aidancrowther/DMX-Now/Docs/priority-packet-substantial-completion.md

# Targeted Priority Packet: Completion

**Status:** Complete for the validated Linux/20 Hz hardware configuration
**Branch:** `master`
**Date:** 2026-09-10

## Scope completed

The targeted priority packet path is implemented across the host daemon,
transmitter, receiver, and shared protocol:

- Added distinct priority and priority-completion packet types.
- Added host-to-transmitter management commands for priority marking and ACK
  retrieval.
- Added complete-universe priority transmission with repeat count, TTL, and
  bounded queueing.
- Added receiver-targeted transaction sequencing and per-receiver state.
- Added receiver completion ACK handling, duplicate/invalid/unknown ACK
  accounting, and retry/recovery behavior.
- Added runtime receiver hard-gate enforcement using a 512-byte write-permission
  table and a no-gates fast path.
- Added staged priority gate metadata with atomic application after complete
  priority reconstruction.
- Added queue-aware transmitter metadata delivery and explicit gate-application
  completion status.
- Fixed the management-interface crash when editing a hard-locked channel.
- Added lead-in and lead-out timing so priority traffic is separated from the
  normal 20 Hz DMX stream.
- Preserved normal latest-state DMX pacing outside priority transactions.
- Added host tests for service behavior and priority transaction handling.
- Added a hardware transition acceptance runner at
  `Host Software/wireless_dmx_daemon/tests/run_priority_transition.py`.

## Acceptance evidence

The following live hardware tests were completed with normal firmware on the
transmitter and all expected receivers discovered during each run:

### Targeted priority test

- 10 priority events submitted.
- Both receivers acknowledged every event.
- 10/10 first-attempt successes.
- 0 retry-recovered events.
- 0 failed events.
- 0 invalid or unknown ACKs.

### Extended priority soak

- 20 events with 10-second spacing.
- 20/20 first-attempt successes.
- Both receivers acknowledged every event.
- 0 retry-recovered events.
- 0 failed events.
- 0 invalid or unknown ACKs.
- Process exit status: `0`.

The final lab soak reported zero failed events, retry recoveries, invalid ACKs,
unknown ACKs, and retry failures. Duplicate ACK records were expected repeated physical completion
records from the receiver ACK-repeat mechanism.

### Priority-to-normal transition

The transition runner uses three separate Mega measurement windows:

1. Normal DMX output before priority.
2. Priority DMX output while the transaction is active.
3. Normal DMX output after ACK completion and a three-second settling period.

The final run passed all phases:

```text
normal before: 222 checks, 222 pass, 0 fail
priority:      311 checks, 311 pass, 0 fail
normal after:  355 checks, 355 pass, 0 fail
receiver ACKs: both expected receivers acknowledged
exit code:     0
```

The post-priority settling period is intentional. An earlier version measured
immediately at the end of the transaction and captured six transient settling
frames. Extending the settle period makes the test distinguish a bounded
transition from a persistent failure to resume normal DMX.

### Hard-gate transition

All expected receivers were included in event construction and required to
report gate application. The Mega monitor validated the physical output through the
lock and unlock transitions:

```text
normal baseline:        266 checks, 266 pass, 0 fail
priority gate establish: 266 checks, 266 pass, 0 fail
normal while locked:    266 checks, 266 pass, 0 fail
priority unlock:        267 checks, 267 pass, 0 fail
normal after unlock:    266 checks, 266 pass, 0 fail
```

Lock and unlock transactions completed on the first attempt with
`PRIORITY_COMPLETE_GATE_APPLIED` from all expected receivers and zero retries. During
the locked phase, normal packets carrying a different value were transmitted
but the receivers continued outputting the priority value. After the all-clear
priority transaction, normal output resumed.

The current 20-event soak was scoped to the expected receiver set:

```text
events: 20
first-attempt successes: 20
failed events: 0
unknown ACKs: 0
invalid ACKs: 0
retry failures: 0
```

## Automated validation

The host test suite passes in full after the current implementation changes:

```text
68 passed
```

The transition runner passes Python compilation and repository whitespace
validation.

## Running the transition test

With the transmitter and monitor connected to the selected host devices, and
the expected receiver IDs discovered or supplied for the run, execute:

```bash
cd "Host Software/wireless_dmx_daemon"
python Tests/run_priority_transition.py \
  --tx-port /dev/ttyUSB0 \
  --mega-port /dev/ttyUSB1 \
  --expected-receiver <receiver-id> \
  --output /tmp/priority-transition.json
```

The command returns zero only when normal output is valid before and after the
priority transaction, the priority output is observed, and every expected
receiver completes the transaction.

## Hardware intervention and resilience validation

The following recovery tests passed with the expected receiver set powered and online:

* receiver removal for 20 seconds followed by reconnection;
* transmitter reset while the daemon remained running;
* clean daemon stop/restart with cache clear and receiver rediscovery;
* controlled PTY client disconnect for 10 seconds followed by reconnection.

Each recovery returned to valid normal DMX output. Fresh priority transactions
after receiver reconnection, transmitter reset, daemon restart, and PTY
reconnection completed with all expected receiver ACKs on the first attempt and
zero retries.

Reliability and throughput work is complete for the validated Linux/ESP8266/Mega deployment at the
20 Hz production rate. Native Windows/macOS virtual serial support, broader
lighting-application/platform coverage, and longer optional soak runs remain
non-blocking follow-up work.

Other existing project follow-up items remain unchanged, including native
Windows/macOS virtual serial support, broader fault-injection coverage, and a
future GUI.
