aidancrowther/DMX-Now/Host Software/wireless_dmx_daemon/wireless_dmx/app.py

"""Application service coordinating adapters and frontend snapshots."""

from __future__ import annotations

import time
import logging
import random
from dataclasses import replace
from threading import Event, Thread, Lock

from .enttec.parser import EnttecParser
from .artnet import ArtNetListener, ArtNetParser
from .models import (DaemonConfig, DaemonHealth, DaemonMode, DaemonSnapshot, DmxStatistics,
    ChannelGate, ObservedUniverse, PriorityAck, PriorityAckSummary, PriorityStatus, TelemetryStatus,
    RetransmitterTelemetry)
from .pacer import DmxPacer
from .telemetry import TelemetryStore
from .transmitter.connection import TransmitterConnection
from .transmitter.management import (CacheClearedResponse, ManagementParser, PriorityAckReport,
                                     TransmitterModeResponse,
                                      clear_receiver_cache_request, get_priority_acks_request, get_telemetry_request,
                                      get_transmitter_mode_request,
                                      get_observed_universe_request, ObservedUniversePart,
                                      RetransmitterTelemetryReport,
                                      set_retransmitter_input_request, locate_retransmitter_request,
                                      mark_next_priority, set_receiver_failsafe_request, set_receiver_output_request,
                                      locate_receiver_request)
from .protocols import DMX_GATE_MASK_SIZE
from .protocols import PRIORITY_COMPLETE_GATE_APPLIED
from .virtual_serial.factory import create_pty_backend
from .raw_dmx import RawDmxParser


class NullVirtualBackend:
    """No-op backend used when virtual serial input is disabled."""

    path = ""
    client_connected = False
    master_fd = None

    def start(self) -> None:
        pass

    def read(self, size: int = 4096) -> bytes:
        return b""

    def stop(self) -> None:
        pass


class WirelessDmxService:
    def __init__(self, config: DaemonConfig, serial_factory=None, virtual_backend=None) -> None:
        config.validate()
        self.config = config
        self.stats = DmxStatistics()
        self.enttec = EnttecParser(stats=self.stats)
        self.telemetry = TelemetryStore(config.telemetry_stale_seconds, config.telemetry_offline_seconds)
        self.management = ManagementParser()
        self.virtual = virtual_backend or (create_pty_backend(config.virtual_port_path)
                                           if config.virtual_serial_enabled else NullVirtualBackend())
        self.raw_virtual = (create_pty_backend(config.raw_virtual_port_path)
                            if config.raw_virtual_serial_enabled else NullVirtualBackend())
        self.raw_dmx = RawDmxParser(config.raw_virtual_timeout_seconds)
        self.artnet_parser = ArtNetParser(config.artnet_universe, self.stats)
        self.artnet = ArtNetListener(config.artnet_bind_host, config.artnet_port, self.artnet_parser) \
            if config.artnet_enabled else None
        self.transmitter = TransmitterConnection(config, self._on_transmitter_data, serial_factory)
        self.pacer = DmxPacer(
            config.pacer_rate_hz, self._send_universe, self.stats,
            send_priority=self._send_priority_universe,
            on_priority_started=self._on_priority_started,
            on_priority_completed=self._on_priority_completed,
            priority_enabled=config.priority_enabled,
            priority_max_queue_depth=config.priority_max_queue_depth,
            priority_max_repeat_count=config.priority_max_repeat_count,
            priority_max_ttl_seconds=config.priority_max_ttl_seconds,
            priority_lead_in_ms=config.priority_lead_in_ms,
            priority_lead_out_ms=config.priority_lead_out_ms,
            priority_max_consecutive_events=config.priority_max_consecutive_events,
        )
        self.manual_universe = bytearray(512)
        self.observed_universe = ObservedUniverse()
        self._retransmitters: dict[int, tuple[RetransmitterTelemetry, float]] = {}
        self._observed_parts: dict[tuple[int, int], dict[int, ObservedUniversePart]] = {}
        self._observed_part_times: dict[tuple[int, int], float] = {}
        self._last_observed_request = 0.0
        self._channel_gates = [ChannelGate.OPEN] * 512
        self._has_source_blocked_channels = False
        self._hard_gate_metadata_pending = bool(config.locked_channels)
        for channel in config.management_only_channels:
            self._channel_gates[channel - 1] = ChannelGate.MANAGEMENT_ONLY
        for channel in config.locked_channels:
            self._channel_gates[channel - 1] = ChannelGate.LOCKED
        self._refresh_gate_fast_path()
        self._stop = Event()
        self._thread: Thread | None = None
        self._lock = Lock()
        self._health = DaemonHealth.STARTING
        self._last_error: str | None = None
        self._last_telemetry_request = 0.0
        self._last_ack_request = 0.0
        self._telemetry_request_started = 0.0
        self._telemetry_requests_sent = 0
        self._telemetry_reports_received = 0
        self._telemetry_consecutive_failures = 0
        self._telemetry_last_report = 0.0
        self._cache_clear_sent_at = 0.0
        self._cache_clear_acknowledged = False
        self._cache_clear_sent = 0
        self._cache_clear_retries = 0
        self._cache_clear_retry_interval = 0.5
        self._report_parts = {}
        self._report_part_times = {}
        self._priority_submissions: dict[int, float] = {}
        # One accepted ACK is valid per submitted event, receiver, and attempt.
        # Frame sequence is diagnostic only: repeated priority fragments/events
        # can legitimately carry different wireless frame sequences.
        self._priority_events: dict[int, dict] = {}
        # One ACK is retained per submitted event, receiver, and attempt.
        # Retry attempts are distinct evidence and must not be discarded as
        # duplicates of the initial attempt.
        self._priority_acks: dict[tuple[int, int, int], PriorityAck] = {}
        self._priority_ack_summary = PriorityAckSummary()
        self._priority_retry_attempts = 0
        self._priority_retry_recovered = 0
        self._priority_retry_failures = 0
        self._normal_quiet_until = 0.0
        self._priority_output_active = False
        self._failsafe_generation = int(time.time()) & 0xFFFFFFFF
        self._last_failsafe_send = 0.0
        self._logger = logging.getLogger("wireless_dmx.service")
        self._transmitter_mode_acknowledged = False
        self._transmitter_mode_query_pending = False
        self._transmitter_mode_set_pending = False
        self._transmitter_mode_current: int | None = None
        self._transmitter_mode_sync = "pending"
        self._transmitter_mode_request_at = 0.0
        self._last_transmitter_connected = False

    def set_manual_channel(self, channel: int, value: int) -> None:
        if not 1 <= channel <= 512:
            raise ValueError("channel must be 1..512")
        if not 0 <= value <= 255:
            raise ValueError("value must be 0..255")
        # This is a management-originated edit. LOCKED means that ordinary
        # source/retransmitter data cannot overwrite the channel; it does not
        # prevent the management interface from deliberately overriding it.
        self.manual_universe[channel - 1] = value

    def set_manual_universe(self, universe: bytes) -> None:
        if len(universe) != 512:
            raise ValueError("manual universe must contain 512 channels")
        # Full-universe edits are also management-originated and may update
        # hard-locked channels. The gate is enforced when external source data
        # is merged, not when the operator sends an explicit management value.
        self.manual_universe[:] = universe

    def channel_gate(self, channel: int) -> ChannelGate:
        if not 1 <= channel <= 512:
            raise ValueError("channel must be 1..512")
        return self._channel_gates[channel - 1]

    def set_channel_gate(self, channel: int, gate: ChannelGate) -> None:
        if not 1 <= channel <= 512:
            raise ValueError("channel must be 1..512")
        gate = ChannelGate(gate)
        previous = self._channel_gates[channel - 1]
        # In management-only mode the retransmitter is the live source. When
        # an operator establishes a hard lock, capture the value currently
        # shown by that source before future observations are intentionally
        # prevented from changing the channel. Otherwise the local management
        # buffer (often still zero) would become the receiver's locked value.
        if (gate == ChannelGate.LOCKED and previous != ChannelGate.LOCKED and
                self.config.mode == DaemonMode.MANAGEMENT_ONLY):
            self.manual_universe[channel - 1] = self.observed_universe.universe[channel - 1]
        self._channel_gates[channel - 1] = gate
        if previous != self._channel_gates[channel - 1] or gate == ChannelGate.LOCKED:
            self._hard_gate_metadata_pending = True
        self._refresh_gate_fast_path()
        management_only, locked = self.channel_gate_lists()
        self.config = replace(self.config, management_only_channels=management_only,
                              locked_channels=locked)
        self.stats.channel_gate_changes += 1

    def _refresh_gate_fast_path(self) -> None:
        self._has_source_blocked_channels = any(gate != ChannelGate.OPEN
                                                for gate in self._channel_gates)

    def channel_gates_snapshot(self) -> tuple[ChannelGate, ...]:
        return tuple(self._channel_gates)

    def channel_gate_lists(self) -> tuple[tuple[int, ...], tuple[int, ...]]:
        return (tuple(i + 1 for i, gate in enumerate(self._channel_gates)
                      if gate == ChannelGate.MANAGEMENT_ONLY),
                tuple(i + 1 for i, gate in enumerate(self._channel_gates)
                      if gate == ChannelGate.LOCKED))

    def clear_manual_universe(self) -> None:
        # Clearing from the management interface is an explicit override too.
        self.manual_universe[:] = bytes(512)

    def manual_universe_snapshot(self) -> bytes:
        return bytes(self.manual_universe)

    def observed_universe_snapshot(self) -> bytes:
        return self.observed_universe.universe

    def _update_observed_universe(self, universe: bytes, sequence: int, source: str) -> None:
        merged = bytearray(universe)
        for index, gate in enumerate(self._channel_gates):
            if gate == ChannelGate.LOCKED:
                merged[index] = self.manual_universe[index]
        self.observed_universe = ObservedUniverse(bytes(merged), sequence, source,
                                                  time.monotonic(), self.observed_universe.updates + 1)

    def _update_local_observed_universe(self, universe: bytes) -> None:
        self._update_observed_universe(universe, 0, "local transmitter")

    def send_manual(self, priority: bool = False, repeat_count: int | None = None,
                    ttl_seconds: float | None = None, reason: str = "manual dashboard") -> int | None:
        if not priority and self.config.mode == DaemonMode.MANAGEMENT_ONLY:
            self.stats.frames_dropped_by_pacer += 1
            raise RuntimeError("normal DMX transmission is disabled in management-only mode")
        universe = bytes(self.manual_universe)
        self._update_local_observed_universe(universe)
        if priority:
            hard_gate_mask = None
            if self._hard_gate_metadata_pending:
                hard_gate_mask_buffer = bytearray(DMX_GATE_MASK_SIZE)
                for index, gate in enumerate(self._channel_gates):
                    if gate == ChannelGate.LOCKED:
                        hard_gate_mask_buffer[index // 8] |= 1 << (index % 8)
                hard_gate_mask = bytes(hard_gate_mask_buffer)
                self._hard_gate_metadata_pending = False
            physical_repeat_count = repeat_count or self.config.priority_default_repeat_count
            self._normal_quiet_until = max(self._normal_quiet_until,
                time.monotonic() + self.config.priority_normal_quiet_before_ms / 1000.0)
            # The transmitter owns the three physical 1 Hz repeats. The daemon
            # submits one logical universe per attempt only.
            priority_id = self.pacer._priority_id
            self.pacer._priority_id = (priority_id + 1) & 0xFFFFFFFF
            # The marker is deliberately queued ahead of the following
            # complete-universe DMX submission. Existing receivers ignore it.
            self._priority_submissions[priority_id] = time.monotonic()
            self._priority_events[priority_id] = {
                "universe": universe, "repeat_count": physical_repeat_count,
                "hard_gate_mask": hard_gate_mask,
                "ttl_seconds": ttl_seconds or self.config.priority_default_ttl_seconds,
                "reason": reason, "attempt": 1, "last_attempt_at": time.monotonic(),
                "retry_count": 0, "terminal": False, "terminal_reason": None,
                "transmission_complete": False, "ack_complete": False,
                "first_attempt_ack_receivers": set(), "ack_receivers": set(),
                "submitted_at": time.monotonic(), "ack_completed_at": None,
                "expected_receivers": set(receiver.receiver_id for receiver in self.telemetry.snapshot()
                                           if receiver.link_state.value == "online"),
                "retry_due_at": None,
                "receiver_states": {receiver.receiver_id: {"attempt": 0, "started_at": None,
                    "ack": False, "failed": False} for receiver in
                    self.telemetry.snapshot() if receiver.link_state.value == "online"},
                "receiver_order": [receiver.receiver_id for receiver in self.telemetry.snapshot()
                                   if receiver.link_state.value == "online"],
                "receiver_index": 0, "current_receiver": None,
            }
            event = self._priority_events[priority_id]
            if event["receiver_order"]:
                self._start_priority_receiver(event, priority_id, time.monotonic())
            else:
                # Preserve the existing broadcast behavior when no fresh
                # receiver telemetry is available (including unit-test and
                # hardware-discovery bootstrap conditions).
                self.transmitter.send_immediate(mark_next_priority(
                    priority_id, physical_repeat_count, 1, 0, hard_gate_mask))
                self.pacer.submit_priority(universe, repeat_count=1,
                                           ttl_seconds=event["ttl_seconds"],
                                           reason=event["reason"], priority_id=priority_id)
            return priority_id
        self.pacer.submit(universe)
        return None

    def set_receiver_output(self, enabled: bool, receiver_id: int = 0) -> tuple[int, ...]:
        """Request a targeted or broadcast MAX3485 output change."""
        online = tuple(receiver.receiver_id for receiver in self.telemetry.snapshot()
                       if receiver.link_state.value == "online" and
                       (receiver_id == 0 or receiver.receiver_id == receiver_id))
        generation = int(time.time() * 1000) & 0xFFFFFFFF
        if receiver_id and not online:
            raise ValueError(f"receiver {receiver_id:08X} is not online")
        if not self.transmitter.connected:
            detail = self.transmitter.last_error or "serial transmitter is not connected"
            raise RuntimeError(f"output control not sent: {detail}")
        if not self.transmitter.send_priority_management(
                set_receiver_output_request(enabled, receiver_id, generation)):
            detail = self.transmitter.last_error or "priority management queue rejected the packet"
            raise RuntimeError(f"output control not sent: {detail}")
        return online

    def locate_receiver(self, receiver_id: int = 0, duration_seconds: int = 15) -> tuple[int, ...]:
        online = tuple(receiver.receiver_id for receiver in self.telemetry.snapshot()
                       if receiver.link_state.value == "online" and
                       (receiver_id == 0 or receiver.receiver_id == receiver_id))
        if receiver_id and not online:
            raise ValueError(f"receiver {receiver_id:08X} is not online")
        generation = int(time.time() * 1000) & 0xFFFFFFFF
        if not self.transmitter.connected:
            detail = self.transmitter.last_error or "serial transmitter is not connected"
            raise RuntimeError(f"locate not sent: {detail}")
        if not self.transmitter.send_priority_management(
                locate_receiver_request(receiver_id, duration_seconds, generation)):
            detail = self.transmitter.last_error or "priority management queue rejected the packet"
            raise RuntimeError(f"locate not sent: {detail}")
        return online

    def set_retransmitter_input(self, enabled: bool, retransmitter_id: int = 0) -> None:
        if not self.config.retransmitter_input_control_enabled:
            raise RuntimeError("retransmitter input control is disabled in configuration")
        generation = int(time.time() * 1000) & 0xFFFFFFFF
        if not self.transmitter.connected:
            raise RuntimeError("retransmitter input control: transmitter is disconnected")
        if not self.transmitter.send_priority_management(
                set_retransmitter_input_request(retransmitter_id, enabled, generation)):
            raise RuntimeError(self.transmitter.last_error or "retransmitter control queue rejected the packet")

    def locate_retransmitter(self, retransmitter_id: int = 0, duration_seconds: int = 15) -> None:
        generation = int(time.time() * 1000) & 0xFFFFFFFF
        if not self.transmitter.connected:
            raise RuntimeError("retransmitter locate: transmitter is disconnected")
        if not self.transmitter.send_priority_management(
                locate_retransmitter_request(retransmitter_id, duration_seconds, generation)):
            raise RuntimeError(self.transmitter.last_error or "retransmitter control queue rejected the packet")

    def clear_priority(self) -> None:
        self.pacer.clear_priority()

    def seed_priority_ids(self, seed: int) -> None:
        """Set the next priority ID before submitting any priority events."""
        with self.pacer._condition:
            if self.pacer._priority_queue or self.pacer._priority_current is not None:
                raise RuntimeError("cannot seed priority IDs while priority traffic is active")
            self.pacer._priority_id = seed & 0xFFFFFFFF

    def start(self) -> None:
        self.telemetry.clear()
        if self.config.mode == DaemonMode.BRIDGE:
            self.virtual.start()
            self.raw_virtual.start()
            if self.artnet:
                self.artnet.start()
        self.transmitter.start()
        self._send_transmitter_mode_query()
        self.pacer.start()
        self._stop.clear()
        self._thread = Thread(target=self._run, name="wireless-dmx-service", daemon=True)
        self._thread.start()
        self._health = DaemonHealth.RUNNING
        self._logger.info("service_started")

    def stop(self) -> None:
        self._health = DaemonHealth.STOPPING
        self._stop.set()
        if self._thread:
            self._thread.join(timeout=2)
        self.pacer.stop()
        self.transmitter.stop()
        if self.artnet:
            self.artnet.stop()
        if self.config.mode == DaemonMode.BRIDGE:
            self.virtual.stop()
            self.raw_virtual.stop()
        self._logger.info("service_stopped")

    def snapshot(self) -> DaemonSnapshot:
        stats = DmxStatistics(**self.stats.__dict__)
        virtual_path = self.virtual.path if getattr(self.virtual, "master_fd", None) is not None else None
        priority = self.pacer.priority_status()
        ack_summary = self._priority_ack_summary
        priority = PriorityStatus(**{**priority.__dict__,
            "ack_accepted": ack_summary.accepted_count,
            "ack_duplicates": ack_summary.duplicate_count,
            "ack_invalid": ack_summary.invalid_count,
            "ack_unknown": ack_summary.unknown_priority_count,
            "ack_duplicate_records": ack_summary.duplicate_record_count,
            "ack_dropped": ack_summary.dropped_count,
            "ack_window_failures": ack_summary.window_failure_count})
        priority = PriorityStatus(**{**priority.__dict__,
            "ack_records_received": ack_summary.records_received})
        priority = PriorityStatus(**{**priority.__dict__,
            "retry_attempts": self._priority_retry_attempts,
            "retry_recovered": self._priority_retry_recovered,
            "retry_failures": self._priority_retry_failures})
        mode_name = ("management_only" if self._transmitter_mode_current == 1 else
                      "bridge" if self._transmitter_mode_current == 0 else None)
        return DaemonSnapshot(health=self._health, virtual_port=virtual_path,
                              transmitter_connected=self.transmitter.connected,
                              virtual_client_connected=self.virtual.client_connected,
                              dmx=stats, receivers=self.telemetry.snapshot(),
                               priority=priority,
                              observed_universe=self.observed_universe,
                              retransmitters=self._retransmitter_snapshot(),
                              transmitter_mode=mode_name,
                              transmitter_mode_sync=self._transmitter_mode_sync,
                              telemetry=TelemetryStatus(
                                  enabled=self.config.telemetry_enabled,
                                  request_in_flight=self._telemetry_request_started > 0,
                                  requests_sent=self._telemetry_requests_sent,
                                  reports_received=self._telemetry_reports_received,
                                  consecutive_failures=self._telemetry_consecutive_failures,
                                  last_request_age_ms=(int((time.monotonic() - self._telemetry_request_started) * 1000)
                                                       if self._telemetry_request_started else None),
                                  last_report_age_ms=(int((time.monotonic() - self._telemetry_last_report) * 1000)
                                                       if self._telemetry_last_report else None),
                                  cache_clear_sent=self._cache_clear_sent,
                                  cache_clear_acknowledged=self._cache_clear_acknowledged,
                                  cache_clear_age_ms=(int((time.monotonic() - self._cache_clear_sent_at) * 1000)
                                                     if self._cache_clear_sent_at else None),
                                  cache_clear_retries=self._cache_clear_retries),
                              last_error=self._last_error)

    def _retransmitter_snapshot(self) -> tuple[RetransmitterTelemetry, ...]:
        now = time.monotonic()
        result = []
        for telemetry, seen in self._retransmitters.values():
            age = now - seen
            state = (type(telemetry.link_state).ONLINE if age <= self.config.telemetry_stale_seconds
                     else type(telemetry.link_state).STALE if age <= self.config.telemetry_offline_seconds
                     else type(telemetry.link_state).OFFLINE)
            # Retransmitters are discovery devices, not a retained inventory.
            # Only an actively reporting device should populate the dashboard
            # or be eligible for retransmitter controls.
            if state != type(telemetry.link_state).ONLINE:
                continue
            result.append(replace(telemetry, link_state=state,
                                  transmitter_rssi=telemetry.transmitter_rssi))
        return tuple(sorted(result, key=lambda item: item.retransmitter_id))

    def _send_cache_clear(self) -> None:
        self._cache_clear_acknowledged = False
        # Drop host-side discovery immediately; the transmitter clears both
        # receiver and retransmitter tables when it processes this request.
        self.telemetry.clear()
        self._retransmitters.clear()
        self.transmitter.send_immediate(clear_receiver_cache_request())
        self._cache_clear_sent += 1
        self._cache_clear_retries = max(0, self._cache_clear_sent - 1)
        self._cache_clear_sent_at = time.monotonic()
        self._logger.info("receiver_cache_clear_sent attempt=%s", self._cache_clear_sent)

    def _send_transmitter_mode_query(self) -> None:
        if self.transmitter.send_immediate(get_transmitter_mode_request()):
            self._transmitter_mode_query_pending = True
            self._transmitter_mode_set_pending = False
            self._transmitter_mode_request_at = time.monotonic()
            self._logger.info("transmitter_mode_query_sent")

    def _send_transmitter_mode(self) -> None:
        from .transmitter.management import set_transmitter_mode_request
        mode = 1 if self.config.mode == DaemonMode.MANAGEMENT_ONLY else 0
        if self.transmitter.send_immediate(set_transmitter_mode_request(mode)):
            self._transmitter_mode_acknowledged = False
            self._transmitter_mode_query_pending = False
            self._transmitter_mode_set_pending = True
            self._logger.info("transmitter_mode_requested mode=%s", self.config.mode.value)

    def _send_universe(self, universe: bytes) -> None:
        if self.config.mode == DaemonMode.MANAGEMENT_ONLY:
            self.stats.frames_dropped_by_pacer += 1
            return
        if self._priority_output_active or time.monotonic() < self._normal_quiet_until:
            self.stats.frames_dropped_by_pacer += 1
            return
        from .enttec.protocol import encode_dmx
        self._update_local_observed_universe(universe)
        self.transmitter.send_latest(encode_dmx(universe))

    def _send_priority_universe(self, universe: bytes) -> None:
        from .enttec.protocol import encode_dmx
        self._update_local_observed_universe(universe)
        self.transmitter.send_latest(encode_dmx(universe))

    def _start_priority_receiver(self, event: dict, priority_id: int, now: float) -> None:
        order = event.get("receiver_order", [])
        while event["receiver_index"] < len(order):
            receiver_id = order[event["receiver_index"]]
            state = event["receiver_states"][receiver_id]
            if state["ack"] or state["failed"]:
                event["receiver_index"] += 1
                continue
            if state["attempt"] >= self.config.priority_max_attempts:
                state["failed"] = True
                event["receiver_index"] += 1
                continue
            state["attempt"] += 1
            state["started_at"] = now
            event["current_receiver"] = receiver_id
            if not self.transmitter.send_priority_management(mark_next_priority(
                priority_id, event["repeat_count"], state["attempt"], receiver_id,
                event["hard_gate_mask"])):
                state["started_at"] = now
                return
            self.pacer.submit_priority(event["universe"], repeat_count=1,
                                       ttl_seconds=event["ttl_seconds"],
                                       reason=event["reason"], priority_id=priority_id,
                                       attempt=state["attempt"],
                                       target_receiver_id=receiver_id)
            return
        event["ack_complete"] = all(state["ack"] for state in event["receiver_states"].values())
        event["transmission_complete"] = True
        event["terminal_reason"] = "ack_complete" if event["ack_complete"] else "receiver_timeout"
        event["terminal"] = True

    def _on_priority_started(self) -> None:
        self._priority_output_active = True

    def _on_priority_completed(self) -> None:
        self._priority_output_active = False
        self._normal_quiet_until = max(self._normal_quiet_until,
            time.monotonic() + self.config.priority_normal_quiet_after_ms / 1000.0)

    def _accept_source_frame(self, universe: bytes, source: str) -> None:
        if self.config.mode == DaemonMode.MANAGEMENT_ONLY:
            self.stats.source_frames_rejected += 1
            self.stats.frames_dropped_by_pacer += 1
            return
        policy = self.config.input_source_policy
        if policy != "latest" and policy != source:
            self.stats.source_frames_rejected += 1
            return
        if source == "artnet":
            self.stats.artnet_source_frames += 1
        elif source == "raw_serial":
            self.stats.raw_serial_source_frames += 1
        else:
            self.stats.serial_source_frames += 1
        if not self._has_source_blocked_channels:
            self.manual_universe[:] = universe
            if self.config.pacer_enabled:
                self.pacer.submit(bytes(universe))
            else:
                self._send_universe(bytes(universe))
                self.stats.frames_submitted += 1
            return
        merged = bytearray(self.manual_universe)
        blocked = 0
        for index, value in enumerate(universe):
            if self._channel_gates[index] == ChannelGate.OPEN:
                merged[index] = value
            else:
                blocked += 1
        self.manual_universe[:] = merged
        if source == "artnet":
            self.stats.artnet_channels_blocked += blocked
        elif source == "raw_serial":
            self.stats.raw_serial_channels_blocked += blocked
        else:
            self.stats.serial_channels_blocked += blocked
        if self.config.pacer_enabled:
            self.pacer.submit(bytes(merged))
        else:
            self._send_universe(bytes(merged))
            self.stats.frames_submitted += 1

    def _on_transmitter_data(self, data: bytes) -> None:
        for part in self.management.feed(data):
            if isinstance(part, RetransmitterTelemetryReport):
                telemetry = part.telemetry
                # The transmitter uses an empty record when no active
                # retransmitter is cached. It must never become a device entry.
                if (telemetry.retransmitter_id == 0 or
                        telemetry.transmitter_last_seen_ms > int(self.config.telemetry_offline_seconds * 1000)):
                    continue
                previous = self._retransmitters.get(telemetry.retransmitter_id)
                # A transmitter can republish the same cached retransmitter
                # record on every management poll. Do not refresh liveness for
                # an unchanged telemetry sequence; freshness must represent a
                # newly broadcast retransmitter packet.
                if (previous is None or
                        telemetry.telemetry_sequence != previous[0].telemetry_sequence or
                        telemetry.uptime_seconds < previous[0].uptime_seconds):
                    self._retransmitters[telemetry.retransmitter_id] = (telemetry, time.monotonic())
                else:
                    self._retransmitters[telemetry.retransmitter_id] = (telemetry, previous[1])
                self._update_management_confirmations()
                continue
            if isinstance(part, ObservedUniversePart):
                key = (part.sequence, part.part_count)
                observed = self._observed_parts.setdefault(key, {})
                observed[part.part_index] = part
                self._observed_part_times.setdefault(key, time.monotonic())
                if len(observed) == part.part_count:
                    ordered = [observed[index] for index in range(part.part_count)]
                    if (ordered[0].offset == 0 and
                            ordered[-1].offset + len(ordered[-1].data) == 512 and
                            all(left.offset + len(left.data) == right.offset
                                for left, right in zip(ordered, ordered[1:])) and
                            len(b"".join(item.data for item in ordered)) == 512 and
                            all(item.source_mac == ordered[0].source_mac and
                                item.sequence == ordered[0].sequence for item in ordered)):
                        self._update_observed_universe(
                            b"".join(item.data for item in ordered),
                            ordered[0].sequence, "retransmitter")
                    self._observed_parts.pop(key, None)
                    self._observed_part_times.pop(key, None)
                continue
            if isinstance(part, CacheClearedResponse):
                self._cache_clear_acknowledged = True
                self.telemetry.clear()
                self._retransmitters.clear()
                self._report_parts.clear()
                self._report_part_times.clear()
                self._logger.info("telemetry_cache_cleared")
                continue
            if isinstance(part, TransmitterModeResponse):
                requested = 1 if self.config.mode == DaemonMode.MANAGEMENT_ONLY else 0
                self._transmitter_mode_current = part.mode
                self._transmitter_mode_query_pending = False
                if part.mode == requested and part.accepted:
                    self._transmitter_mode_acknowledged = True
                    self._transmitter_mode_set_pending = False
                    self._transmitter_mode_sync = "synchronized"
                    if self._health == DaemonHealth.TRANSMITTER_MODE_REJECTED:
                        self._health = DaemonHealth.RUNNING
                        self._last_error = None
                    self._send_cache_clear()
                elif part.mode != requested and part.accepted:
                    self._send_transmitter_mode()
                else:
                    self._transmitter_mode_acknowledged = False
                    self._transmitter_mode_set_pending = False
                    self._transmitter_mode_sync = "rejected"
                    active = "management_only" if part.mode == 1 else "bridge" if part.mode == 0 else f"unknown({part.mode})"
                    requested_name = "management_only" if requested == 1 else "bridge"
                    self._last_error = (f"transmitter rejected requested mode {requested_name}; "
                                        f"active mode remains {active} (possibly statically locked)")
                    self._health = DaemonHealth.TRANSMITTER_MODE_REJECTED
                self._logger.info("transmitter_mode_response accepted=%s mode=%s",
                                  part.accepted, part.mode)
                continue
            if isinstance(part, PriorityAckReport):
                self._consume_priority_ack_report(part)
                continue
            report = self._report_parts.setdefault(part.report_sequence, {})
            report[part.part_index] = part
            self._report_part_times.setdefault(part.report_sequence, time.monotonic())
            if len(report) == part.part_count:
                if self.telemetry.update_report(tuple(report[index] for index in range(part.part_count))):
                    self._logger.info("telemetry_report_received sequence=%s parts=%s", part.report_sequence, part.part_count)
                    self._telemetry_reports_received += 1
                    self._telemetry_consecutive_failures = 0
                    self._telemetry_last_report = time.monotonic()
                    self._telemetry_request_started = 0.0
                    self._update_management_confirmations()
                del self._report_parts[part.report_sequence]
                del self._report_part_times[part.report_sequence]

    def _update_management_confirmations(self) -> None:
        """Complete output/locate management events from fresh telemetry state."""
        receivers = {item.receiver_id: item for item in self.telemetry.snapshot()}
        retransmitters = {item.retransmitter_id: item for item in self._retransmitter_snapshot()}
        for event in self._priority_events.values():
            if event.get("management_complete") or event.get("terminal"):
                continue
            operation = event.get("management_operation")
            desired = event.get("management_enabled")
            confirmed = set(event.get("ack_receivers", set()))
            for kind, device_id in event.get("management_targets", ()):
                item = receivers.get(device_id) if kind == "receiver" else retransmitters.get(device_id)
                if item is None or item.link_state.value != "online":
                    continue
                if operation == "output":
                    state = item.output_enabled if kind == "receiver" else item.input_enabled
                    if state == desired:
                        confirmed.add(device_id)
                elif operation == "locate" and item.locate_active:
                    confirmed.add(device_id)
            event["ack_receivers"] = confirmed
            expected = set(event.get("expected_receivers", set()))
            if expected and expected.issubset(confirmed):
                event["management_complete"] = True
                event["terminal"] = True
                event["transmission_complete"] = True
                event["terminal_reason"] = "telemetry_confirmed"

    def _consume_priority_ack_report(self, report: PriorityAckReport) -> None:
        previous = self._priority_ack_summary
        duplicate_records = previous.duplicate_record_count
        unknown = previous.unknown_priority_count
        window_failures = previous.window_failure_count
        for raw in report.records:
            received = PriorityAck(**{**raw.__dict__, "received_monotonic": time.monotonic()})
            key = (received.priority_id, received.receiver_id, received.attempt)
            if key in self._priority_acks:
                duplicate_records += 1
                continue
            self._priority_acks[key] = received
            event = self._priority_events.get(received.priority_id)
            if event is not None and received.attempt > 1:
                event["recovered"] = True
                self._priority_retry_recovered += 1
            if event is not None:
                event.setdefault("ack_receivers", set()).add(received.receiver_id)
                if received.completion_status == PRIORITY_COMPLETE_GATE_APPLIED:
                    event.setdefault("gate_applied_receivers", set()).add(received.receiver_id)
                if received.attempt == 1:
                    event.setdefault("first_attempt_ack_receivers", set()).add(received.receiver_id)
                expected = event["expected_receivers"]
                state = event.get("receiver_states", {}).get(received.receiver_id)
                gate_ack_valid = (
                    event.get("hard_gate_mask") is None or
                    received.completion_status == PRIORITY_COMPLETE_GATE_APPLIED
                )
                if state is not None and gate_ack_valid:
                    state["ack"] = True
                    state["failed"] = False
                    if event.get("current_receiver") == received.receiver_id:
                        event["receiver_index"] += 1
                        self._start_priority_receiver(event, received.priority_id, time.monotonic())
                completion_receivers = (
                    event.get("gate_applied_receivers", set())
                    if event.get("hard_gate_mask") is not None
                    else event["ack_receivers"]
                )
                if expected and expected.issubset(completion_receivers):
                    event["ack_complete"] = True
                    event["ack_completed_at"] = event.get("ack_completed_at") or time.monotonic()
                    event["terminal"] = True
                    event["transmission_complete"] = True
                    event["terminal_reason"] = "ack_complete"
            submitted = self._priority_submissions.get(received.priority_id)
            if submitted is None:
                unknown += 1
            elif (received.ack_delay_ms != 0xFFFF and
                  received.ack_delay_ms > self.config.priority_confirmation_window_ms):
                window_failures += 1
        self._priority_ack_summary = PriorityAckSummary(
            accepted_count=report.accepted_count,
            duplicate_count=report.duplicate_count,
            invalid_count=report.invalid_count,
            dropped_count=report.dropped_count,
            records_received=sum(1 for _ in self._priority_acks),
            unknown_priority_count=unknown,
            duplicate_record_count=duplicate_records,
            window_failure_count=window_failures,
        )

    def _run(self) -> None:
        while not self._stop.is_set():
            try:
                connected = self.transmitter.connected
                if connected and not self._last_transmitter_connected:
                    self._send_transmitter_mode_query()
                self._last_transmitter_connected = connected
                incoming = self.virtual.read()
                if incoming:
                    for frame in self.enttec.feed(incoming):
                        self._accept_source_frame(frame.universe(), "serial")
                raw_incoming = self.raw_virtual.read()
                if self.raw_dmx.expire():
                    self.stats.raw_serial_timeout_drops += 1
                if raw_incoming:
                    for frame in self.raw_dmx.feed(raw_incoming):
                        self._accept_source_frame(frame.data, "raw_serial")
                if self.artnet:
                    for frame in self.artnet.receive():
                        data = frame.data + bytes(512 - len(frame.data))
                        self._accept_source_frame(data, "artnet")
                now = time.monotonic()
                self._service_priority_retries(now)
                if (self._transmitter_mode_query_pending and
                        now - self._transmitter_mode_request_at >= self._cache_clear_retry_interval):
                    self._send_transmitter_mode_query()
                if not self._transmitter_mode_acknowledged:
                    # Do not send fail-safe, telemetry, or ACK-poll traffic
                    # until the transmitter role has been discovered and, if
                    # necessary, changed to match the daemon configuration.
                    if (not self._transmitter_mode_query_pending and
                            not self._transmitter_mode_set_pending):
                        self._send_transmitter_mode_query()
                    time.sleep(0.001)
                    continue
                if not self._cache_clear_acknowledged:
                    if (now - self._cache_clear_sent_at >= self._cache_clear_retry_interval):
                        self._send_cache_clear()
                    # Do not poll telemetry or priority ACKs until the
                    # transmitter has confirmed that its receiver cache is
                    # empty. Otherwise the first report can be old cache data.
                    time.sleep(0.001)
                    continue
                if now - self._last_failsafe_send >= 1.0:
                    self.transmitter.send_priority_management(set_receiver_failsafe_request(
                        getattr(self.config.receiver_failsafe_mode, "value", self.config.receiver_failsafe_mode),
                        self.config.receiver_failsafe_timeout_seconds,
                        self._failsafe_generation))
                    self._last_failsafe_send = now
                for sequence, started in list(self._report_part_times.items()):
                    if now - started > self.config.telemetry_max_report_age_seconds:
                        self._report_parts.pop(sequence, None)
                        self._report_part_times.pop(sequence, None)
                for key, started in list(self._observed_part_times.items()):
                    if now - started > 2.0:
                        self._observed_parts.pop(key, None)
                        self._observed_part_times.pop(key, None)
                if self.config.telemetry_enabled and now - self._last_telemetry_request >= self.config.telemetry_interval_seconds:
                    if (self._telemetry_request_started and
                            now - self._telemetry_request_started >= self.config.telemetry_response_timeout_seconds):
                        self._telemetry_consecutive_failures += 1
                        self._telemetry_request_started = 0.0
                    self.transmitter.send_immediate(get_telemetry_request())
                    self._last_telemetry_request = now
                    self._telemetry_request_started = now
                    self._telemetry_requests_sent += 1
                if now - self._last_ack_request >= 0.1:
                    self.transmitter.send_immediate(get_priority_acks_request())
                    self._last_ack_request = now
                if (self.config.mode == DaemonMode.MANAGEMENT_ONLY and
                        now - self._last_observed_request >= 0.25):
                    self.transmitter.send_immediate(get_observed_universe_request())
                    self._last_observed_request = now
            except Exception as exc:
                self._last_error = str(exc)
                self._health = DaemonHealth.TELEMETRY_DEGRADED
            else:
                if not self.transmitter.connected:
                    self._health = DaemonHealth.TRANSMITTER_DISCONNECTED
                elif self._health in (DaemonHealth.TRANSMITTER_DISCONNECTED, DaemonHealth.TELEMETRY_DEGRADED):
                    self._health = DaemonHealth.RUNNING
            time.sleep(0.001)

    def _service_priority_retries(self, now: float) -> None:
        # The ACK delay is measured at the transmitter, but the daemon receives
        # the exported record on a later management poll and the pacer may have
        # queued a retry behind the current priority event. Give every attempt
        # one full confirmation window plus a bounded export/drain grace period.
        window = max(self.config.priority_confirmation_window_ms / 1000.0, 1.0)
        for priority_id, event in list(self._priority_events.items()):
            if event["terminal"] or now - event["last_attempt_at"] < window:
                continue
            if event.get("receiver_order"):
                current = event.get("current_receiver")
                if current is None:
                    self._start_priority_receiver(event, priority_id, now)
                    continue
                state = event["receiver_states"][current]
                if state["ack"]:
                    event["receiver_index"] += 1
                    event["current_receiver"] = None
                    self._start_priority_receiver(event, priority_id, now)
                    continue
                started = state["started_at"] or event["submitted_at"]
                receiver_deadline = (
                    started + self.config.priority_receiver_budget_seconds +
                    self.config.priority_lead_in_ms / 1000.0 +
                    self.config.priority_confirmation_window_ms / 1000.0 +
                    0.5
                )
                if now >= receiver_deadline:
                    if state["attempt"] < self.config.priority_max_attempts:
                        # Retry the same receiver inside its transaction budget;
                        # do not mark it failed until all configured attempts
                        # have been exhausted.
                        state["started_at"] = now
                        self._priority_retry_attempts += 1
                        event["retry_count"] += 1
                        event["last_attempt_at"] = now
                        self._start_priority_receiver(event, priority_id, now)
                    else:
                        state["failed"] = True
                        event["receiver_index"] += 1
                        event["current_receiver"] = None
                        self._start_priority_receiver(event, priority_id, now)
                continue
            expected = event["expected_receivers"]
            if not expected:
                expected.update(receiver.receiver_id for receiver in self.telemetry.snapshot()
                                if receiver.link_state.value == "online")
            received_ids = {key[1] for key in self._priority_acks if key[0] == priority_id}
            if expected and expected.issubset(received_ids):
                event["ack_complete"] = True
                event["transmission_complete"] = True
                event["terminal_reason"] = "ack_complete"
                event["terminal"] = True
                continue
            if event["retry_due_at"] is None:
                event["retry_due_at"] = now + random.uniform(
                    self.config.priority_retry_cooldown_min_seconds,
                    self.config.priority_retry_cooldown_max_seconds)
                continue
            if now < event["retry_due_at"]:
                continue
            if event["attempt"] < self.config.priority_max_attempts:
                with self.pacer._condition:
                    if self.pacer._priority_current is not None or self.pacer._priority_queue:
                        continue
                next_attempt = event["attempt"] + 1
                try:
                    self.pacer.submit_priority(event["universe"], 1,
                                               event["ttl_seconds"], event["reason"],
                                               priority_id=priority_id, attempt=next_attempt)
                    if not self.transmitter.send_priority_management(mark_next_priority(
                            priority_id, event["repeat_count"], next_attempt,
                            event.get("current_receiver") or 0,
                            event.get("hard_gate_mask"))):
                        event["last_attempt_at"] = now
                        continue
                    event["attempt"] = next_attempt
                    event["retry_count"] += 1
                    event["last_attempt_at"] = now
                    event["retry_due_at"] = None
                    self._priority_retry_attempts += 1
                except (OverflowError, RuntimeError):
                    event["last_attempt_at"] = now
            else:
                if now - event["last_attempt_at"] >= window * 2.0:
                    event["transmission_complete"] = True
                    event["terminal_reason"] = "ack_timeout"
                    event["terminal"] = True
                    self._priority_retry_failures += 1
