aidancrowther/DMX-Now/Host Software/wireless_dmx_daemon/wireless_dmx/transmitter/management.py

"""Feature 11 management frame codec."""

from __future__ import annotations

import struct
from dataclasses import dataclass

from ..models import PriorityAck, ReceiverLinkState, ReceiverTelemetry, RetransmitterTelemetry
from ..protocols import (
    MANAGEMENT_GET_RECEIVER_TELEMETRY, MANAGEMENT_PROTO_VERSION,
    MANAGEMENT_MARK_NEXT_PRIORITY,
    MANAGEMENT_GET_PRIORITY_ACKS, MANAGEMENT_PRIORITY_ACKS,
    MANAGEMENT_CLEAR_RECEIVER_CACHE, MANAGEMENT_CACHE_CLEARED,
    MANAGEMENT_SET_RECEIVER_FAILSAFE,
    MANAGEMENT_SET_RECEIVER_OUTPUT, MANAGEMENT_LOCATE_RECEIVER,
    MANAGEMENT_SET_TRANSMITTER_MODE, MANAGEMENT_TRANSMITTER_MODE,
    MANAGEMENT_GET_TRANSMITTER_MODE,
    MANAGEMENT_GET_OBSERVED_UNIVERSE, MANAGEMENT_OBSERVED_UNIVERSE,
    MANAGEMENT_RETRANSMITTER_TELEMETRY, MANAGEMENT_RETRANSMITTER_CONTROL,
    MANAGEMENT_RECEIVER_TELEMETRY, MANAGEMENT_SYNC, ProtocolError, crc16_ccitt,
)
from ..protocols import DMX_GATE_MASK_SIZE

PART_HEADER = struct.Struct("<BBBBI")
RECORD = struct.Struct("<I6sBBbb7I HBBIBB HII BBBBI".replace(" ", ""))
ACK_HEADER = struct.Struct("<BBIIIII")
ACK_RECORD = struct.Struct("<I I I BBBb I H".replace(" ", ""))


@dataclass(frozen=True)
class TelemetryReportPart:
    report_version: int
    part_index: int
    part_count: int
    report_sequence: int
    records: tuple[ReceiverTelemetry, ...]


@dataclass(frozen=True)
class PriorityAckReport:
    report_sequence: int
    accepted_count: int
    duplicate_count: int
    invalid_count: int
    dropped_count: int
    records: tuple[PriorityAck, ...]


@dataclass(frozen=True)
class CacheClearedResponse:
    acknowledged: bool = True


@dataclass(frozen=True)
class TransmitterModeResponse:
    status: int
    mode: int

    @property
    def accepted(self) -> bool:
        return self.status == 0


@dataclass(frozen=True)
class ObservedUniversePart:
    part_index: int
    part_count: int
    sequence: int
    age_ms: int
    offset: int
    source_mac: bytes
    data: bytes


@dataclass(frozen=True)
class RetransmitterTelemetryReport:
    telemetry: RetransmitterTelemetry


def get_telemetry_request() -> bytes:
    body = bytes((MANAGEMENT_PROTO_VERSION, MANAGEMENT_GET_RECEIVER_TELEMETRY, 0, 0))
    return MANAGEMENT_SYNC + body + struct.pack("<H", crc16_ccitt(body))


def get_priority_acks_request() -> bytes:
    body = bytes((MANAGEMENT_PROTO_VERSION, MANAGEMENT_GET_PRIORITY_ACKS, 0, 0))
    return MANAGEMENT_SYNC + body + struct.pack("<H", crc16_ccitt(body))


def clear_receiver_cache_request() -> bytes:
    body = bytes((MANAGEMENT_PROTO_VERSION, MANAGEMENT_CLEAR_RECEIVER_CACHE, 0, 0))
    return MANAGEMENT_SYNC + body + struct.pack("<H", crc16_ccitt(body))


def set_transmitter_mode_request(mode: int) -> bytes:
    if mode not in (0, 1):
        raise ValueError("transmitter mode must be 0 (bridge) or 1 (management-only)")
    payload = bytes((mode,))
    body = bytes((MANAGEMENT_PROTO_VERSION, MANAGEMENT_SET_TRANSMITTER_MODE)) + struct.pack("<H", 1) + payload
    return MANAGEMENT_SYNC + body + struct.pack("<H", crc16_ccitt(body))


def get_transmitter_mode_request() -> bytes:
    body = bytes((MANAGEMENT_PROTO_VERSION, MANAGEMENT_GET_TRANSMITTER_MODE, 0, 0))
    return MANAGEMENT_SYNC + body + struct.pack("<H", crc16_ccitt(body))


def get_observed_universe_request() -> bytes:
    body = bytes((MANAGEMENT_PROTO_VERSION, MANAGEMENT_GET_OBSERVED_UNIVERSE, 0, 0))
    return MANAGEMENT_SYNC + body + struct.pack("<H", crc16_ccitt(body))


def set_retransmitter_input_request(target_id: int, enabled: bool, generation: int) -> bytes:
    payload = struct.pack("<IBI", target_id & 0xFFFFFFFF, int(enabled), generation & 0xFFFFFFFF)
    body = bytes((MANAGEMENT_PROTO_VERSION, MANAGEMENT_RETRANSMITTER_CONTROL)) + struct.pack("<H", len(payload)) + payload
    return MANAGEMENT_SYNC + body + struct.pack("<H", crc16_ccitt(body))


def locate_retransmitter_request(target_id: int, duration_seconds: int = 15,
                                 generation: int = 0) -> bytes:
    if not 1 <= duration_seconds <= 15:
        raise ValueError("locate duration must be between 1 and 15 seconds")
    payload = struct.pack("<IHI", target_id & 0xFFFFFFFF, duration_seconds,
                          generation & 0xFFFFFFFF)
    body = bytes((MANAGEMENT_PROTO_VERSION, MANAGEMENT_RETRANSMITTER_CONTROL)) + struct.pack("<H", len(payload)) + payload
    return MANAGEMENT_SYNC + body + struct.pack("<H", crc16_ccitt(body))


def set_receiver_failsafe_request(mode: str, timeout_seconds: int, generation: int) -> bytes:
    modes = {"hold": 0, "blackout": 1, "disable_line": 2}
    if mode not in modes:
        raise ValueError("unsupported receiver fail-safe mode")
    payload = struct.pack("<BBHI", modes[mode], 0, timeout_seconds, generation & 0xFFFFFFFF)
    body = bytes((MANAGEMENT_PROTO_VERSION, MANAGEMENT_SET_RECEIVER_FAILSAFE)) + struct.pack("<H", len(payload)) + payload
    return MANAGEMENT_SYNC + body + struct.pack("<H", crc16_ccitt(body))


def set_receiver_output_request(enabled: bool, target_receiver_id: int, generation: int) -> bytes:
    payload = struct.pack("<BBI", 1 if enabled else 0, 0, target_receiver_id & 0xFFFFFFFF)
    payload += struct.pack("<I", generation & 0xFFFFFFFF)
    body = bytes((MANAGEMENT_PROTO_VERSION, MANAGEMENT_SET_RECEIVER_OUTPUT)) + struct.pack("<H", len(payload)) + payload
    return MANAGEMENT_SYNC + body + struct.pack("<H", crc16_ccitt(body))


def locate_receiver_request(target_receiver_id: int, duration_seconds: int = 15, generation: int = 0) -> bytes:
    if not 1 <= duration_seconds <= 15:
        raise ValueError("locate duration must be between 1 and 15 seconds")
    payload = struct.pack("<IHI", target_receiver_id & 0xFFFFFFFF, duration_seconds,
                          generation & 0xFFFFFFFF)
    body = bytes((MANAGEMENT_PROTO_VERSION, MANAGEMENT_LOCATE_RECEIVER)) + struct.pack("<H", len(payload)) + payload
    return MANAGEMENT_SYNC + body + struct.pack("<H", crc16_ccitt(body))


def mark_next_priority(priority_id: int, repeat_count: int = 3, attempt: int = 1,
                       target_receiver_id: int = 0,
                       hard_gate_mask: bytes | None = None) -> bytes:
    """Tell the transmitter to classify the next complete ENTTEC universe."""
    if hard_gate_mask is None:
        payload = struct.pack("<IIBB", priority_id & 0xFFFFFFFF,
                              target_receiver_id & 0xFFFFFFFF,
                              repeat_count & 0xFF, attempt & 0xFF)
    else:
        if len(hard_gate_mask) != DMX_GATE_MASK_SIZE:
            raise ValueError("hard gate mask must contain 64 bytes")
        payload = struct.pack("<IIBBB", priority_id & 0xFFFFFFFF,
                              target_receiver_id & 0xFFFFFFFF,
                              repeat_count & 0xFF, attempt & 0xFF, 1) + hard_gate_mask
    body = bytes((MANAGEMENT_PROTO_VERSION, MANAGEMENT_MARK_NEXT_PRIORITY)) + struct.pack("<H", len(payload)) + payload
    return MANAGEMENT_SYNC + body + struct.pack("<H", crc16_ccitt(body))


def _frame(payload: bytes, opcode: int = MANAGEMENT_RECEIVER_TELEMETRY) -> bytes:
    body = bytes((MANAGEMENT_PROTO_VERSION, opcode)) + struct.pack("<H", len(payload)) + payload
    return MANAGEMENT_SYNC + body + struct.pack("<H", crc16_ccitt(body))


def parse_management_frame(frame: bytes):
    if len(frame) < 8 or frame[:2] != MANAGEMENT_SYNC:
        raise ProtocolError("invalid management frame")
    version, opcode = frame[2:4]
    length = struct.unpack_from("<H", frame, 4)[0]
    if version != MANAGEMENT_PROTO_VERSION:
        raise ProtocolError("unexpected management response")
    if len(frame) != 8 + length:
        raise ProtocolError("management length mismatch")
    if crc16_ccitt(frame[2:6 + length]) != struct.unpack_from("<H", frame, 6 + length)[0]:
        raise ProtocolError("management CRC mismatch")
    if opcode == MANAGEMENT_PRIORITY_ACKS:
        if length < ACK_HEADER.size:
            raise ProtocolError("missing priority ACK header")
        report_version, record_count, sequence, accepted, duplicates, invalid, dropped = ACK_HEADER.unpack_from(frame, 6)
        if report_version != 1 or record_count > 9 or length != ACK_HEADER.size + record_count * ACK_RECORD.size:
            raise ProtocolError("invalid priority ACK report")
        records = []
        for offset in range(6 + ACK_HEADER.size, 6 + length, ACK_RECORD.size):
            values = ACK_RECORD.unpack_from(frame, offset)
            records.append(PriorityAck(*values, received_monotonic=0.0))
        return PriorityAckReport(sequence, accepted, duplicates, invalid, dropped, tuple(records))
    if opcode == MANAGEMENT_CACHE_CLEARED:
        if length != 0:
            raise ProtocolError("invalid cache clear response")
        return CacheClearedResponse()
    if opcode == MANAGEMENT_TRANSMITTER_MODE:
        if length != 2:
            raise ProtocolError("invalid transmitter mode response")
        return TransmitterModeResponse(frame[6], frame[7])
    if opcode == MANAGEMENT_OBSERVED_UNIVERSE:
        header = struct.Struct("<BBBBIIH6s")
        if length < header.size:
            raise ProtocolError("missing observed universe part header")
        version, index, count, _, sequence, age_ms, offset, source_mac = header.unpack_from(frame, 6)
        data = frame[6 + header.size:6 + length]
        if version != 1 or count == 0 or index >= count or offset + len(data) > 512:
            raise ProtocolError("invalid observed universe part")
        return ObservedUniversePart(index, count, sequence, age_ms, offset, source_mac, data)
    if opcode == MANAGEMENT_RETRANSMITTER_TELEMETRY:
        # The transmitter forwards the complete packed
        # RetransmitterTelemetryPacket, including its DMX protocol header,
        # followed by the transmitter RSSI and cache age.  Keep the header in
        # this layout; otherwise valid firmware reports are silently rejected
        # by the length check below.
        record = struct.Struct("<HBBBI6sII5BH10IbI")
        if length != record.size:
            raise ProtocolError("invalid retransmitter telemetry report")
        f = record.unpack_from(frame, 6)
        if f[0] != 0x444D or f[1] != 1 or f[2] != 12 or f[3] != 1:
            raise ProtocolError("invalid retransmitter telemetry packet")
        battery = {0: "ok", 1: "low", 255: "unknown"}.get(f[10], "unknown")
        telemetry = RetransmitterTelemetry(
            retransmitter_id=f[4], mac_address=f[5].hex(":"),
            link_state=ReceiverLinkState.ONLINE, transmitter_rssi=f[24],
            uptime_seconds=f[6], telemetry_sequence=f[7], transmitter_last_seen_ms=f[25], input_enabled=bool(f[8]),
            input_signal_active=bool(f[9]), battery_state=battery,
            locate_active=bool(f[11]), input_hardware_control_available=bool(f[12]),
            learned_input_slots=f[13], time_since_last_input_ms=f[14],
            input_frames_received=f[15], input_frames_skipped=f[16],
            invalid_start_codes=f[17], invalid_lengths=f[18],
            wireless_frame_sequence=f[19], wireless_frames_sent=f[20],
            wireless_send_failures=f[21], missed_deadlines=f[22],
            control_generation=f[23])
        return RetransmitterTelemetryReport(telemetry)
    if opcode != MANAGEMENT_RECEIVER_TELEMETRY:
        raise ProtocolError("unexpected management response")
    if length < PART_HEADER.size:
        raise ProtocolError("missing telemetry part header")
    report_version, index, count, record_count, sequence = PART_HEADER.unpack_from(frame, 6)
    if count == 0 or index >= count or record_count > 3:
        raise ProtocolError("invalid telemetry part indexes")
    record_data = frame[6 + PART_HEADER.size:6 + length]
    if len(record_data) != record_count * RECORD.size:
        raise ProtocolError("invalid telemetry record count")
    records = []
    for offset in range(0, len(record_data), RECORD.size):
        f = RECORD.unpack_from(record_data, offset)
        records.append(ReceiverTelemetry(
            receiver_id=f[0], mac_address=f[1].hex(":"),
            link_state=ReceiverLinkState({1: "online", 2: "stale", 3: "offline"}.get(f[2], "unknown")),
            battery_low=bool(f[3]), transmitter_rssi=f[4], receiver_last_rssi=f[5],
            uptime_seconds=f[6], last_active_sequence=f[7], complete_universes=f[8],
            incomplete_universes=f[9], malformed_packets=f[10], time_since_last_universe_ms=f[11],
            transmitter_last_seen_ms=f[12], firmware_version=f[13], protocol_version=f[14],
            # f[15] is the packed record's reserved byte; telemetrySequence is
            # f[16]. The remaining fields are the receiver fail-safe status.
            # fresh receiver reports from being mistaken for sequence zero.
            telemetry_sequence=f[16], failsafe_mode={0: "hold", 1: "blackout", 2: "disable_line"}.get(f[17], "hold"),
            failsafe_active=bool(f[18]), failsafe_timeout_seconds=f[19],
            failsafe_generation=f[20], failsafe_activations=f[21],
            output_override_active=bool(f[22]), output_enabled=bool(f[23]),
            locate_active=bool(f[24]), hard_gates_active=bool(f[25]),
            output_control_generation=f[26],
        ))
    return TelemetryReportPart(report_version, index, count, sequence, tuple(records))


class ManagementParser:
    """Streaming parser for management responses using a bounded buffer."""

    def __init__(self, max_payload: int = 240) -> None:
        self.max_payload = max_payload
        self._buffer = bytearray()

    def feed(self, data: bytes) -> list[TelemetryReportPart]:
        self._buffer.extend(data)
        parts: list[TelemetryReportPart] = []
        while True:
            start = self._buffer.find(MANAGEMENT_SYNC)
            if start < 0:
                if self._buffer[-1:] == MANAGEMENT_SYNC[:1]:
                    self._buffer[:] = self._buffer[-1:]
                else:
                    self._buffer.clear()
                return parts
            del self._buffer[:start]
            if len(self._buffer) < 6:
                return parts
            length = self._buffer[4] | self._buffer[5] << 8
            if length > self.max_payload:
                del self._buffer[0]
                continue
            total = 8 + length
            if len(self._buffer) < total:
                return parts
            frame = bytes(self._buffer[:total])
            del self._buffer[:total]
            try:
                parts.append(parse_management_frame(frame))
            except ProtocolError:
                continue
