aidancrowther/DMX-Now/Host Software/wireless_dmx_daemon/tests/test_dashboard.py

import os
import sys
import unittest
import tempfile
from pathlib import Path

sys.path.insert(0, str(Path(__file__).parents[1]))

import wireless_dmx.dashboard as dashboard_module
from wireless_dmx.dashboard import (ADVANCED_COMMANDS, MAIN_COMMANDS, MANUAL_COMMANDS, SETUP_COMMANDS,
                                    DashboardController, bar, build_parser, channel_gate_color,
                                    channel_gate_selected_color,
                                      manual_priority_locked, priority_feedback, receiver_display_segments,
                                       retransmitter_display_headers, retransmitter_display_lines,
                                       format_age_ms, rssi_quality, _read_line_blocking)
from wireless_dmx.models import (ChannelGate, DaemonConfig, DaemonMode, ReceiverLinkState,
                                 ReceiverTelemetry, RetransmitterTelemetry)
from wireless_dmx.config import apply_args


class DashboardTests(unittest.TestCase):
    def test_format_age_switches_to_seconds_after_99999ms(self):
        self.assertEqual(format_age_ms(99999), "99999ms")
        self.assertEqual(format_age_ms(100000), "100.0s")
        self.assertEqual(format_age_ms(0xFFFFFFFF), "never")

    def test_retransmitter_display_exposes_input_and_wireless_counters(self):
        retransmitter = RetransmitterTelemetry(
            7, "18:fe:34:00:00:07", ReceiverLinkState.ONLINE, -42, 100, 8, 12,
            True, True, "unknown", False, False, 512, 25, 1000, 2, 3, 4,
            19, 1000, 1, 2, 0,
        )
        first = retransmitter_display_lines(retransmitter)
        self.assertIn("-42dBm", first)
        self.assertIn("12ms", first)
        self.assertIn("512", first)
        self.assertIn("RTX-00000007", first)
        self.assertIn("1000", retransmitter_display_lines(retransmitter, view=1))
        self.assertIn("19", retransmitter_display_lines(retransmitter, view=2))

    def test_retransmitter_headers_align_with_both_data_lines(self):
        retransmitter = RetransmitterTelemetry(
            7, "18:fe:34:00:00:07", ReceiverLinkState.ONLINE, -42, 100, 8, 12,
            True, True, "unknown", False, False, 512, 25, 1000, 2, 3, 4,
            19, 1000, 1, 2, 0,
        )
        for view in range(3):
            header = retransmitter_display_headers(view)
            data = retransmitter_display_lines(retransmitter, view=view)
            self.assertEqual(len(header), len(data))
        for label in ("NAME/ID", "LINK", "RSSI", "REPORT AGE", "INPUT", "SIGNAL", "SLOTS", "BATTERY", "LOCATE"):
            self.assertIn(label, retransmitter_display_headers(0))
        for label in ("UPTIME", "TELEM SEQ", "INPUT AGE", "RX FRAMES", "SKIPPED", "BAD START", "BAD LENGTH"):
            self.assertIn(label, retransmitter_display_headers(1))

    def test_settings_input_uses_blocking_read_mode(self):
        class FakeWindow:
            def __init__(self):
                self.calls = []

            def nodelay(self, value):
                self.calls.append(("nodelay", value))

            def timeout(self, value):
                self.calls.append(("timeout", value))

            def getstr(self, y, x, width):
                self.calls.append(("getstr", y, x, width))
                return b"value"

        window = FakeWindow()
        original_echo = dashboard_module.curses.echo
        original_noecho = dashboard_module.curses.noecho
        original_curs_set = dashboard_module.curses.curs_set
        try:
            dashboard_module.curses.echo = lambda: window.calls.append(("echo",))
            dashboard_module.curses.noecho = lambda: window.calls.append(("noecho",))
            dashboard_module.curses.curs_set = lambda value: window.calls.append(("curs_set", value))
            self.assertEqual(_read_line_blocking(window, 5, 10, 80), "value")
        finally:
            dashboard_module.curses.echo = original_echo
            dashboard_module.curses.noecho = original_noecho
            dashboard_module.curses.curs_set = original_curs_set
        self.assertIn(("nodelay", False), window.calls)
        self.assertIn(("timeout", -1), window.calls)
        self.assertIn(("nodelay", True), window.calls)
        self.assertIn(("timeout", 250), window.calls)

    def test_dashboard_parser_defaults(self):
        args = build_parser().parse_args([])
        self.assertEqual(args.mega_port, "/dev/ttyUSB1")
        self.assertFalse(args.no_daemon)

    def test_dashboard_parser_documents_and_applies_transmitter_modes(self):
        management_args = build_parser().parse_args(["--management-only"])
        bridge_args = build_parser().parse_args(["--bridge-mode"])
        self.assertTrue(management_args.management_only)
        self.assertTrue(bridge_args.bridge_mode)
        self.assertEqual(apply_args(DaemonConfig(mode=DaemonMode.BRIDGE), management_args).mode,
                         DaemonMode.MANAGEMENT_ONLY)
        self.assertEqual(apply_args(DaemonConfig(mode=DaemonMode.MANAGEMENT_ONLY), bridge_args).mode,
                         DaemonMode.BRIDGE)

    def test_controller_starts_without_hardware_when_not_started(self):
        controller = DashboardController(DaemonConfig(virtual_port_path="/tmp/dashboard-test"))
        try:
            self.assertIsNone(controller.service)
            self.assertIn("dashboard", controller.events) if controller.events else None
        finally:
            controller.close()

    def test_management_only_dashboard_starts_without_pty_path_error(self):
        config = DaemonConfig(mode=DaemonMode.MANAGEMENT_ONLY,
                              virtual_serial_enabled=False,
                              raw_virtual_serial_enabled=False,
                              artnet_enabled=False)
        controller = DashboardController(config)
        try:
            controller.start_daemon()
            self.assertIn("PTY=-", controller.events[0])
        finally:
            controller.close()

    def test_manual_editor_locks_priority_in_management_only_mode(self):
        self.assertTrue(manual_priority_locked(DaemonConfig(mode=DaemonMode.MANAGEMENT_ONLY)))
        self.assertFalse(manual_priority_locked(DaemonConfig(mode=DaemonMode.BRIDGE)))

    def test_default_config_is_read_only_and_save_as_switches_file(self):
        with tempfile.TemporaryDirectory() as directory:
            controller = DashboardController(DaemonConfig(), config_path="default.conf")
            try:
                with self.assertRaises(PermissionError):
                    controller.save_configuration()
                with self.assertRaises(PermissionError):
                    controller.save_as(str(Path(directory) / "default.conf"))
                target = str(Path(directory) / "show.toml")
                controller.save_as(target)
                self.assertEqual(controller.config_path, target)
                self.assertTrue(Path(target).exists())
                self.assertIn("configuration saved as", controller.events[0])
            finally:
                controller.close()

    def test_visualization_helpers_are_bounded(self):
        self.assertEqual(bar(0, 100, 8), "[........]")
        self.assertEqual(bar(100, 100, 8), "[########]")
        self.assertEqual(bar(200, 100, 8), "[########]")
        self.assertEqual(rssi_quality(-30)[0], "GOOD")
        self.assertEqual(rssi_quality(-90)[0], "WEAK")

    def test_channel_gate_colors_are_consistent(self):
        self.assertEqual(channel_gate_color(ChannelGate.OPEN), "muted")
        self.assertEqual(channel_gate_color(ChannelGate.MANAGEMENT_ONLY), "warning")
        self.assertEqual(channel_gate_color(ChannelGate.LOCKED), "critical")
        self.assertEqual(channel_gate_selected_color(ChannelGate.OPEN), "gate_open_selected")
        self.assertEqual(channel_gate_selected_color(ChannelGate.MANAGEMENT_ONLY), "gate_management_selected")
        self.assertEqual(channel_gate_selected_color(ChannelGate.LOCKED), "gate_locked_selected")

    def test_low_battery_field_does_not_overlap_rssi_field(self):
        receiver = ReceiverTelemetry(
            7, "18:fe:34:00:00:07", ReceiverLinkState.ONLINE, True,
            -39, -40, 1, 2, 3, 4, 0, 5, 6, 1, 1, 0,
        )
        receiver_id, link, battery, rssi, counters = receiver_display_segments(receiver)
        self.assertEqual(battery, "LOW")
        self.assertIn("-39dBm", rssi)
        self.assertIn("GOOD", rssi)
        self.assertNotIn("LOW", rssi)
        self.assertIn("6ms", counters)
        self.assertIn("FS:hold/60s", counters)

    def test_receiver_output_display_is_only_on_or_off(self):
        receiver = ReceiverTelemetry(
            7, "18:fe:34:00:00:07", ReceiverLinkState.ONLINE, False,
            -39, -40, 1, 2, 3, 4, 0, 5, 6, 1, 1, 0,
            "hold", False, 60, 0, 0, True, False, False, True, 1,
        )
        line = dashboard_module.receiver_table_line(receiver)
        self.assertIn("OUTPUT:OFF", line)
        self.assertNotIn("OVERRIDE", line)

    def test_receiver_display_includes_friendly_name_and_id(self):
        receiver = ReceiverTelemetry(
            7, "18:fe:34:00:00:07", ReceiverLinkState.ONLINE, False,
            -39, -40, 1, 2, 3, 4, 0, 5, 6, 1, 1, 0,
        )
        identity, *_ = receiver_display_segments(receiver, {7: "Front Truss"})
        self.assertEqual(identity, "Front Truss      [00000007]")

    def test_long_receiver_display_name_scrolls_in_sixteen_character_window(self):
        receiver = ReceiverTelemetry(
            7, "18:fe:34:00:00:07", ReceiverLinkState.ONLINE, False,
            -39, -40, 1, 2, 3, 4, 0, 5, 6, 1, 1, 0,
        )
        first, *_ = receiver_display_segments(receiver, {7: "A very long receiver name"}, now=0.0)
        second, *_ = receiver_display_segments(receiver, {7: "A very long receiver name"}, now=3.0)
        self.assertEqual(len(first), 27)
        self.assertEqual(len(second), 27)
        self.assertNotEqual(first, second)
        self.assertIn("[00000007]", first)

    def test_all_dashboard_command_legends_include_settings(self):
        self.assertIn("[s]", MAIN_COMMANDS)
        self.assertIn("SETTINGS", MAIN_COMMANDS)
        self.assertIn("[u]", MAIN_COMMANDS)
        self.assertIn("MANUAL DMX", MAIN_COMMANDS)
        self.assertIn("[n] names", MAIN_COMMANDS)
        self.assertIn("[o] RX/TX control", MAIN_COMMANDS)
        self.assertIn("[i] locate", MAIN_COMMANDS)
        self.assertIn("DMX", MAIN_COMMANDS)
        self.assertIn("[p] priority", MAIN_COMMANDS)
        self.assertIn("[a]", MANUAL_COMMANDS)
        self.assertIn("[z] reset zero", MANUAL_COMMANDS)
        self.assertIn("[r] repeats", MANUAL_COMMANDS)
        self.assertIn("[t] TTL", MANUAL_COMMANDS)
        self.assertIn("[0-9] type value", MANUAL_COMMANDS)
        self.assertIn("[Enter] apply/send", MANUAL_COMMANDS)
        self.assertNotIn("[o] output", MANUAL_COMMANDS)
        self.assertNotIn("[i] locate", MANUAL_COMMANDS)
        self.assertIn("[q] quit", MANUAL_COMMANDS)
        self.assertIn("[w]", SETUP_COMMANDS)
        self.assertIn("[e] edit", SETUP_COMMANDS)
        self.assertIn("[a] Save As", SETUP_COMMANDS)
        self.assertIn("[q] quit", SETUP_COMMANDS)
        self.assertIn("[x]", ADVANCED_COMMANDS)
        self.assertIn("[l]", MANUAL_COMMANDS)

    def test_priority_feedback_lists_acknowledged_receivers(self):
        text = priority_feedback({
            "priority_id": 42,
            "expected_receivers": {7, 9},
            "ack_receivers": {7},
            "gate_applied_receivers": {7},
            "hard_gate_mask": bytes(64),
            "ack_complete": False,
            "terminal": False,
            "retry_count": 1,
        })
        self.assertIn("PRIORITY 42 WAITING", text)
        self.assertIn("ACK 00000007", text)
        self.assertIn("EXPECT 00000007,00000009", text)
        self.assertIn("GATE 00000007", text)

    def test_management_feedback_is_complete_not_failed(self):
        for action in ("OUTPUT", "LOCATE"):
            text = priority_feedback({
                "priority_id": action,
                "expected_receivers": {0xDB07D7},
                "ack_receivers": {0xDB07D7},
                "retry_count": 0,
                "management_complete": True,
                "terminal": True,
                "terminal_reason": "management packet sent",
            })
            self.assertIn(f"PRIORITY {action} COMPLETE", text)
            self.assertNotIn("FAILED", text)

    def test_pending_priority_feedback_does_not_report_completion(self):
        event = {"priority_id": "OUTPUT", "expected_receivers": {7, 9},
                 "ack_receivers": {7}, "management_complete": False,
                 "terminal": False, "retry_count": 0}
        self.assertIn("WAITING", priority_feedback(event))


if __name__ == "__main__":
    unittest.main()
