aidancrowther/DMX-Now/Host Software/wireless_dmx_daemon/tests/test_service.py

import os
import struct
import sys
import time
import unittest
from pathlib import Path

sys.path.insert(0, str(Path(__file__).parents[1]))

from wireless_dmx.app import WirelessDmxService
from wireless_dmx.enttec.protocol import encode_dmx
from wireless_dmx.raw_dmx import RAW_DMX_UNIVERSE_SIZE
from wireless_dmx.models import (ChannelGate, DaemonConfig, DaemonMode, ReceiverLinkState,
                                 ReceiverTelemetry, RetransmitterTelemetry)
from wireless_dmx.protocols import (MANAGEMENT_CACHE_CLEARED, MANAGEMENT_OBSERVED_UNIVERSE,
                                    MANAGEMENT_PRIORITY_ACKS, MANAGEMENT_RECEIVER_TELEMETRY,
                                    MANAGEMENT_RETRANSMITTER_TELEMETRY,
                                    MANAGEMENT_SYNC, crc16_ccitt)
from wireless_dmx.transmitter.management import ACK_HEADER, ACK_RECORD, PART_HEADER, RECORD
from wireless_dmx.virtual_serial.linux_pty import LinuxPtyBackend


class FakeSerial:
    def __init__(self):
        self.writes = []
        self.closed = False
        self.reads = []

    def write(self, data):
        self.writes.append(bytes(data))
        return len(data)

    def read(self, size=1):
        return self.reads.pop(0) if self.reads else b""

    def close(self):
        self.closed = True


def telemetry_part():
    record = RECORD.pack(7, bytes.fromhex("18fe34000007"), 1, 0, -25, -30,
                         100, 9, 10, 1, 0, 2, 100, 1, 1, 0, 4, 0, 0, 60, 0, 0,
                         0, 1, 0, 0, 0)
    payload = PART_HEADER.pack(1, 0, 1, 1, 4) + record
    body = bytes((1, MANAGEMENT_RECEIVER_TELEMETRY)) + struct.pack("<H", len(payload)) + payload
    return MANAGEMENT_SYNC + body + struct.pack("<H", crc16_ccitt(body))


class ServiceTests(unittest.TestCase):
    @staticmethod
    def retransmitter_report(retransmitter_id=7, age_ms=50, sequence=3):
        packet = struct.Struct("<HBBBI6sII5BH10IbI").pack(
            0x444D, 1, 12, 1, retransmitter_id, bytes.fromhex("18fe34000007"),
            10, sequence, 1, 1, 255, 0, 1, 512, age_ms, 10, 0, 0, 0, 1, 2, 3, 4, 5,
            -40, age_ms)
        body = bytes((1, MANAGEMENT_RETRANSMITTER_TELEMETRY)) + struct.pack("<H", len(packet)) + packet
        return MANAGEMENT_SYNC + body + struct.pack("<H", crc16_ccitt(body))

    @staticmethod
    def cache_cleared_response():
        body = bytes((1, MANAGEMENT_CACHE_CLEARED, 0, 0))
        return MANAGEMENT_SYNC + body + struct.pack("<H", crc16_ccitt(body))

    def test_cache_clear_removes_receivers_and_retransmitters(self):
        service = WirelessDmxService(
            DaemonConfig(mode=DaemonMode.MANAGEMENT_ONLY, virtual_serial_enabled=False,
                         raw_virtual_serial_enabled=False, artnet_enabled=False, virtual_port_path=""),
            serial_factory=lambda: FakeSerial())
        service._on_transmitter_data(self.retransmitter_report())
        self.assertEqual(len(service._retransmitters), 1)
        service._send_cache_clear()
        self.assertEqual(service._retransmitters, {})
        service._on_transmitter_data(self.cache_cleared_response())
        self.assertEqual(service._retransmitters, {})

    def test_stale_retransmitter_report_does_not_populate_active_devices(self):
        service = WirelessDmxService(
            DaemonConfig(mode=DaemonMode.MANAGEMENT_ONLY, virtual_serial_enabled=False,
                         raw_virtual_serial_enabled=False, artnet_enabled=False, virtual_port_path=""),
            serial_factory=lambda: FakeSerial())
        service._on_transmitter_data(self.retransmitter_report(age_ms=31_000))
        self.assertEqual(service._retransmitters, {})
        self.assertEqual(service.snapshot().retransmitters, ())

    def test_active_retransmitter_report_populates_devices(self):
        service = WirelessDmxService(
            DaemonConfig(mode=DaemonMode.MANAGEMENT_ONLY, virtual_serial_enabled=False,
                         raw_virtual_serial_enabled=False, artnet_enabled=False, virtual_port_path=""),
            serial_factory=lambda: FakeSerial())
        service._on_transmitter_data(self.retransmitter_report(age_ms=50))
        retransmitters = service.snapshot().retransmitters
        self.assertEqual(len(retransmitters), 1)
        self.assertEqual(retransmitters[0].retransmitter_id, 7)
        self.assertEqual(retransmitters[0].link_state, ReceiverLinkState.ONLINE)

    def test_retransmitter_duplicate_telemetry_does_not_refresh_freshness(self):
        service = WirelessDmxService(
            DaemonConfig(mode=DaemonMode.MANAGEMENT_ONLY, virtual_serial_enabled=False,
                         raw_virtual_serial_enabled=False, artnet_enabled=False, virtual_port_path=""),
            serial_factory=lambda: FakeSerial())
        telemetry = RetransmitterTelemetry(7, "18:fe:34:00:00:07", ReceiverLinkState.ONLINE,
                                           -40, 10, 3, 5, True, True)
        service._retransmitters[7] = (telemetry, time.monotonic() - 20)
        service._on_transmitter_data(b"")
        service._retransmitters[7] = (telemetry, service._retransmitters[7][1])
        self.assertGreater(time.monotonic() - service._retransmitters[7][1], 19)

    def test_retransmitter_controls_queue_without_receiver_telemetry(self):
        fake = FakeSerial()
        service = WirelessDmxService(
            DaemonConfig(mode=DaemonMode.MANAGEMENT_ONLY, virtual_serial_enabled=False,
                         raw_virtual_serial_enabled=False, artnet_enabled=False, virtual_port_path="",
                         retransmitter_input_control_enabled=True),
            serial_factory=lambda: fake)
        service.transmitter.connected = True
        service.set_retransmitter_input(False, 0x00FDA976)
        service.locate_retransmitter(0x00FDA976, 15)
        self.assertEqual(len(service.transmitter._priority_management_queue.queue), 2)

    def test_observed_universe_preserves_hard_gates_and_does_not_pace(self):
        service = WirelessDmxService(
            DaemonConfig(mode=DaemonMode.MANAGEMENT_ONLY, virtual_serial_enabled=False,
                         raw_virtual_serial_enabled=False, artnet_enabled=False, virtual_port_path=""),
            serial_factory=lambda: FakeSerial())
        service.set_manual_channel(2, 99)
        service.set_channel_gate(2, ChannelGate.LOCKED)
        header = struct.Struct("<BBBBIIH6s")
        universe = bytes([10, 20, 30]) + bytes(509)
        for index, offset in enumerate((0, 180, 360)):
            data = universe[offset:offset + (180 if index < 2 else 152)]
            payload = header.pack(1, index, 3, 0, 12, 1, offset, bytes.fromhex("18fe34000001")) + data
            body = bytes((1, MANAGEMENT_OBSERVED_UNIVERSE)) + struct.pack("<H", len(payload)) + payload
            frame = MANAGEMENT_SYNC + body + struct.pack("<H", crc16_ccitt(body))
            service._on_transmitter_data(frame)
        observed = service.observed_universe_snapshot()
        self.assertEqual(observed[0], 10)
        self.assertEqual(observed[1], 0)
        self.assertEqual(observed[2], 30)
        self.assertEqual(service.pacer.priority_status().queue_depth, 0)

    def test_management_editor_can_override_hard_locked_channel(self):
        service = WirelessDmxService(
            DaemonConfig(mode=DaemonMode.MANAGEMENT_ONLY, virtual_serial_enabled=False,
                         raw_virtual_serial_enabled=False, artnet_enabled=False, virtual_port_path=""),
            serial_factory=lambda: FakeSerial())
        service.set_channel_gate(2, ChannelGate.LOCKED)
        service.set_manual_channel(2, 123)
        self.assertEqual(service.manual_universe_snapshot()[1], 123)
        service.set_manual_universe(bytes([45]) * 512)
        self.assertEqual(service.manual_universe_snapshot()[1], 45)

    def test_external_source_still_cannot_override_hard_locked_channel(self):
        service = WirelessDmxService(
            DaemonConfig(virtual_serial_enabled=False, raw_virtual_serial_enabled=False,
                         artnet_enabled=True, virtual_port_path=""),
            serial_factory=lambda: FakeSerial())
        service.set_channel_gate(2, ChannelGate.LOCKED)
        service.set_manual_channel(2, 123)
        service._accept_source_frame(bytes([45]) * 512, "serial")
        self.assertEqual(service.manual_universe_snapshot()[1], 123)

    def test_management_lock_captures_current_observed_value(self):
        service = WirelessDmxService(
            DaemonConfig(mode=DaemonMode.MANAGEMENT_ONLY, virtual_serial_enabled=False,
                         raw_virtual_serial_enabled=False, artnet_enabled=False, virtual_port_path=""),
            serial_factory=lambda: FakeSerial())
        service._update_observed_universe(bytes([7, 88]) + bytes(510), 12, "retransmitter")
        self.assertEqual(service.manual_universe_snapshot()[1], 0)
        service.set_channel_gate(2, ChannelGate.LOCKED)
        self.assertEqual(service.manual_universe_snapshot()[1], 88)
        service._update_observed_universe(bytes([9, 33]) + bytes(510), 13, "retransmitter")
        self.assertEqual(service.observed_universe_snapshot()[1], 88)
    def test_management_only_rejects_normal_source_and_manual_send(self):
        service = WirelessDmxService(
            DaemonConfig(mode=DaemonMode.MANAGEMENT_ONLY, virtual_serial_enabled=False,
                         raw_virtual_serial_enabled=False, artnet_enabled=False, virtual_port_path=""),
            serial_factory=lambda: FakeSerial())
        universe = bytes([55]) * 512
        service._accept_source_frame(universe, "serial")
        self.assertEqual(service.stats.source_frames_rejected, 1)
        self.assertEqual(service.manual_universe_snapshot(), bytes(512))
        with self.assertRaises(RuntimeError):
            service.send_manual(priority=False)

    def test_management_only_preserves_priority_submission(self):
        service = WirelessDmxService(
            DaemonConfig(mode=DaemonMode.MANAGEMENT_ONLY, virtual_serial_enabled=False,
                         raw_virtual_serial_enabled=False, artnet_enabled=False, virtual_port_path=""),
            serial_factory=lambda: FakeSerial())
        priority_id = service.send_manual(priority=True)
        self.assertEqual(priority_id, 0)
        self.assertEqual(service.pacer.priority_status().queue_depth, 1)

    def test_management_only_does_not_start_dmx_backends(self):
        service = WirelessDmxService(
            DaemonConfig(mode=DaemonMode.MANAGEMENT_ONLY, virtual_serial_enabled=True,
                         raw_virtual_serial_enabled=True, artnet_enabled=True),
            serial_factory=lambda: FakeSerial())
        service.start()
        try:
            self.assertIsNone(service.virtual.master_fd)
            self.assertIsNone(service.raw_virtual.master_fd)
            self.assertIsNone(service.artnet.socket if service.artnet else None)
        finally:
            service.stop()

    def test_start_queries_transmitter_mode_before_cache_clear(self):
        fake = FakeSerial()
        service = WirelessDmxService(
            DaemonConfig(mode=DaemonMode.MANAGEMENT_ONLY, virtual_serial_enabled=False,
                         raw_virtual_serial_enabled=False, artnet_enabled=False, virtual_port_path=""),
            serial_factory=lambda: fake)
        service.start()
        try:
            deadline = time.monotonic() + 1
            while time.monotonic() < deadline and len(fake.writes) < 2:
                time.sleep(0.01)
            self.assertGreaterEqual(len(fake.writes), 2)
            self.assertEqual(fake.writes[0][3], 0x09)
            self.assertEqual(fake.writes[0][4:6], b"\x00\x00")
            self.assertNotEqual(fake.writes[1][3], 0x04)
        finally:
            service.stop()

    def test_rejected_transmitter_mode_is_reported_as_error(self):
        service = WirelessDmxService(DaemonConfig(mode=DaemonMode.BRIDGE),
                                     serial_factory=lambda: FakeSerial())
        body = bytes((1, 0x88, 2, 0, 1, 1))
        frame = MANAGEMENT_SYNC + body + struct.pack("<H", crc16_ccitt(body))
        service._on_transmitter_data(frame)
        snapshot = service.snapshot()
        self.assertEqual(snapshot.health.value, "transmitter_mode_rejected")
        self.assertEqual(snapshot.transmitter_mode, "management_only")
        self.assertEqual(snapshot.transmitter_mode_sync, "rejected")
        self.assertIn("rejected requested mode bridge", snapshot.last_error)

    def test_service_accepts_raw_dmx_universe(self):
        backend = LinuxPtyBackend()
        raw_backend = LinuxPtyBackend()
        fake = FakeSerial()
        service = WirelessDmxService(
            DaemonConfig(virtual_serial_enabled=False, raw_virtual_serial_enabled=True,
                         artnet_enabled=False, virtual_port_path="",
                         raw_virtual_port_path="/tmp/raw-dmx-service-test"),
            serial_factory=lambda: fake, virtual_backend=backend)
        service.raw_virtual.stop()
        service.raw_virtual = raw_backend
        service.start()
        try:
            with open(service.raw_virtual.path, "wb", buffering=0) as client:
                client.write(bytes([0x55]) * RAW_DMX_UNIVERSE_SIZE)
            deadline = time.monotonic() + 1
            while time.monotonic() < deadline and service.snapshot().dmx.raw_serial_source_frames < 1:
                time.sleep(0.01)
            self.assertEqual(service.snapshot().dmx.raw_serial_source_frames, 1)
            self.assertEqual(service.manual_universe_snapshot(), bytes([0x55]) * 512)
        finally:
            service.stop()

    def test_service_abandons_timed_out_raw_universe(self):
        fake = FakeSerial()
        service = WirelessDmxService(
            DaemonConfig(virtual_serial_enabled=False, raw_virtual_serial_enabled=True,
                         artnet_enabled=False, virtual_port_path="",
                         raw_virtual_port_path="/tmp/raw-dmx-timeout-test",
                         raw_virtual_timeout_seconds=0.05),
            serial_factory=lambda: fake)
        service.start()
        try:
            with open(service.raw_virtual.path, "wb", buffering=0) as client:
                client.write(bytes([0x11]) * 200)
            time.sleep(0.15)
            self.assertGreaterEqual(service.snapshot().dmx.raw_serial_timeout_drops, 1)
            self.assertEqual(service.manual_universe_snapshot(), bytes(512))
        finally:
            service.stop()
    def test_service_forwards_normalized_pty_dmx_to_fake_transmitter(self):
        backend = LinuxPtyBackend()
        fake = FakeSerial()
        factory = lambda: fake
        # Empty requested path is invalid, so use a temporary PTY without a link.
        config = DaemonConfig(virtual_port_path="/tmp/wireless-dmx-service-test")
        service = WirelessDmxService(config, serial_factory=factory, virtual_backend=backend)
        service.start()
        try:
            with open(backend.path, "wb", buffering=0) as client:
                client.write(encode_dmx(bytes([0x44]) * 512))
                deadline = time.monotonic() + 1
                while time.monotonic() < deadline and service.snapshot().dmx.frames_submitted < 1:
                    time.sleep(0.01)
            deadline = time.monotonic() + 1
            while time.monotonic() < deadline and not any(write.startswith(b"~\x06") for write in fake.writes):
                time.sleep(0.01)
            self.assertTrue(any(write.startswith(b"~\x06") for write in fake.writes))
            self.assertEqual(service.snapshot().dmx.valid_dmx_frames, 1)
        finally:
            service.stop()

    def test_transmitter_management_data_updates_snapshot(self):
        backend = LinuxPtyBackend()
        fake = FakeSerial()
        service = WirelessDmxService(
            DaemonConfig(virtual_port_path="/tmp/wireless-dmx-service-test-2"),
            serial_factory=lambda: fake, virtual_backend=backend)
        service._on_transmitter_data(telemetry_part())
        snapshot = service.snapshot()
        self.assertEqual(len(snapshot.receivers), 1)
        self.assertEqual(snapshot.receivers[0].receiver_id, 7)
        self.assertEqual(snapshot.receivers[0].transmitter_rssi, -25)

    def test_service_start_clears_telemetry_store(self):
        service = WirelessDmxService(DaemonConfig(virtual_port_path="/tmp/wireless-dmx-clear"),
                                     serial_factory=lambda: FakeSerial(),
                                     virtual_backend=LinuxPtyBackend("/tmp/wireless-dmx-clear"))
        service.telemetry.update(ReceiverTelemetry(7, "00:00:00:00:00:07", ReceiverLinkState.ONLINE,
                                                   False, -1, -1, 1, 1, 1, 0, 0, 0, 0, 1, 1, 1))
        service.start()
        try:
            self.assertEqual(service.snapshot().receivers, ())
        finally:
            service.stop()

    def test_service_waits_for_cache_clear_before_polling(self):
        fake = FakeSerial()
        service = WirelessDmxService(DaemonConfig(virtual_port_path="/tmp/wireless-dmx-cache-handshake"),
                                     serial_factory=lambda: fake,
                                     virtual_backend=LinuxPtyBackend("/tmp/wireless-dmx-cache-handshake"))
        service.start()
        try:
            time.sleep(0.05)
            self.assertFalse(service.snapshot().telemetry.cache_clear_acknowledged)
            self.assertFalse(any(write[3] == 0x81 for write in fake.writes if len(write) > 3))
            mode_body = bytes((1, 0x88, 2, 0, 0, 0))
            cache_body = bytes((1, MANAGEMENT_CACHE_CLEARED, 0, 0))
            fake.reads.append(
                MANAGEMENT_SYNC + mode_body + struct.pack("<H", crc16_ccitt(mode_body)) +
                MANAGEMENT_SYNC + cache_body + struct.pack("<H", crc16_ccitt(cache_body)))
            deadline = time.monotonic() + 1
            while time.monotonic() < deadline and not service.snapshot().telemetry.cache_clear_acknowledged:
                time.sleep(0.01)
            self.assertTrue(service.snapshot().telemetry.cache_clear_acknowledged)
            deadline = time.monotonic() + 1
            while time.monotonic() < deadline and service.snapshot().telemetry.requests_sent == 0:
                time.sleep(0.01)
            self.assertGreater(service.snapshot().telemetry.requests_sent, 0)
        finally:
            service.stop()

    def test_priority_ack_updates_snapshot_and_deduplicates_records(self):
        fake = FakeSerial()
        service = WirelessDmxService(DaemonConfig(virtual_port_path="/tmp/wireless-dmx-acks"),
                                     serial_factory=lambda: fake, virtual_backend=LinuxPtyBackend())
        service._priority_submissions[42] = time.monotonic()
        record = ACK_RECORD.pack(42, 7, 99, 1, 1, 3, -41, 1234, 37)
        payload = ACK_HEADER.pack(1, 1, 5, 1, 0, 0, 0) + record
        body = bytes((1, MANAGEMENT_PRIORITY_ACKS)) + struct.pack("<H", len(payload)) + payload
        frame = MANAGEMENT_SYNC + body + struct.pack("<H", crc16_ccitt(body))
        service._on_transmitter_data(frame + frame)
        priority = service.snapshot().priority
        self.assertEqual(priority.ack_accepted, 1)
        self.assertEqual(priority.ack_duplicate_records, 1)
        self.assertEqual(priority.ack_unknown, 0)

    def test_priority_ack_with_new_frame_sequence_is_still_a_duplicate_event(self):
        fake = FakeSerial()
        service = WirelessDmxService(DaemonConfig(virtual_port_path="/tmp/wireless-dmx-acks-seq"),
                                     serial_factory=lambda: fake, virtual_backend=LinuxPtyBackend())
        service._priority_submissions[42] = time.monotonic()
        records = (
            ACK_RECORD.pack(42, 7, 99, 1, 1, 3, -41, 1234, 37),
            ACK_RECORD.pack(42, 7, 100, 1, 1, 3, -41, 1240, 41),
        )
        payload = ACK_HEADER.pack(1, 2, 6, 2, 0, 0, 0) + b"".join(records)
        body = bytes((1, MANAGEMENT_PRIORITY_ACKS)) + struct.pack("<H", len(payload)) + payload
        frame = MANAGEMENT_SYNC + body + struct.pack("<H", crc16_ccitt(body))
        service._on_transmitter_data(frame)
        priority = service.snapshot().priority
        self.assertEqual(priority.ack_accepted, 2)
        self.assertEqual(priority.ack_duplicate_records, 1)

    def test_unmatched_ack_timing_sentinel_is_not_a_window_failure(self):
        fake = FakeSerial()
        service = WirelessDmxService(DaemonConfig(virtual_port_path="/tmp/wireless-dmx-ack-sentinel"),
                                     serial_factory=lambda: fake, virtual_backend=LinuxPtyBackend())
        service._priority_submissions[42] = time.monotonic()
        record = ACK_RECORD.pack(42, 7, 99, 1, 1, 3, -41, 1234, 0xFFFF)
        payload = ACK_HEADER.pack(1, 1, 5, 1, 0, 0, 0) + record
        body = bytes((1, MANAGEMENT_PRIORITY_ACKS)) + struct.pack("<H", len(payload)) + payload
        frame = MANAGEMENT_SYNC + body + struct.pack("<H", crc16_ccitt(body))
        service._on_transmitter_data(frame)
        self.assertEqual(service.snapshot().priority.ack_window_failures, 0)

    def test_manual_channel_and_priority_submission(self):
        fake = FakeSerial()
        service = WirelessDmxService(
            DaemonConfig(virtual_port_path="/tmp/wireless-dmx-manual-test"),
            serial_factory=lambda: fake,
            virtual_backend=LinuxPtyBackend("/tmp/wireless-dmx-manual-test"),
        )
        service.set_manual_channel(1, 255)
        self.assertEqual(service.manual_universe_snapshot()[0], 255)
        with self.assertRaises(ValueError):
            service.set_manual_channel(513, 1)
        priority_id = service.send_manual(priority=True, repeat_count=1, ttl_seconds=1)
        self.assertEqual(priority_id, 0)
        self.assertEqual(service.pacer.priority_status().queue_depth, 1)

    def test_manual_universe_reset_clears_all_channels_without_sending(self):
        service = WirelessDmxService(
            DaemonConfig(virtual_port_path="/tmp/wireless-dmx-reset-test"),
            serial_factory=lambda: FakeSerial(),
            virtual_backend=LinuxPtyBackend("/tmp/wireless-dmx-reset-test"),
        )
        service.set_manual_universe(bytes([99]) * 512)
        service.set_channel_gate(1, ChannelGate.LOCKED)
        service.set_manual_channel(2, 77)
        service.clear_manual_universe()
        self.assertEqual(service.manual_universe_snapshot()[0], 0)
        self.assertEqual(service.manual_universe_snapshot()[1], 0)
        self.assertEqual(service.pacer.priority_status().queue_depth, 0)

    def test_channel_gates_block_external_sources_but_allow_management(self):
        service = WirelessDmxService(
            DaemonConfig(virtual_port_path="/tmp/wireless-dmx-gates"),
            serial_factory=lambda: FakeSerial(), virtual_backend=LinuxPtyBackend(),
        )
        service.set_manual_universe(bytes([10, 20]) + bytes(510))
        service.set_channel_gate(1, ChannelGate.MANAGEMENT_ONLY)
        service.set_channel_gate(2, ChannelGate.LOCKED)
        service._accept_source_frame(bytes([100, 200, 30]) + bytes(509), "serial")
        self.assertEqual(service.manual_universe_snapshot()[:3], bytes([10, 20, 30]))
        service.set_manual_channel(1, 101)
        service.set_manual_channel(2, 201)
        self.assertEqual(service.manual_universe_snapshot()[1], 201)
        self.assertEqual(service.stats.serial_channels_blocked, 2)

    def test_locked_management_edit_is_allowed(self):
        service = WirelessDmxService(
            DaemonConfig(virtual_port_path="/tmp/wireless-dmx-locked-edit"),
            serial_factory=lambda: FakeSerial(), virtual_backend=LinuxPtyBackend(),
        )
        service.set_manual_channel(1, 17)
        service.set_channel_gate(1, ChannelGate.LOCKED)
        service.set_manual_channel(1, 99)
        self.assertEqual(service.manual_universe_snapshot()[0], 99)
        self.assertEqual(service.stats.management_channels_rejected, 0)

    def test_open_source_fast_path_copies_complete_universe(self):
        service = WirelessDmxService(
            DaemonConfig(virtual_port_path="/tmp/wireless-dmx-open-fast-path"),
            serial_factory=lambda: FakeSerial(), virtual_backend=LinuxPtyBackend(),
        )
        universe = bytes(range(256)) * 2
        service._accept_source_frame(universe, "serial")
        self.assertFalse(service._has_source_blocked_channels)
        self.assertEqual(service.manual_universe_snapshot(), universe)

    def test_clear_and_full_management_updates_include_locked_channels(self):
        service = WirelessDmxService(DaemonConfig(virtual_port_path="/tmp/wireless-dmx-gates-2"),
                                     serial_factory=lambda: FakeSerial(), virtual_backend=LinuxPtyBackend())
        service.set_manual_channel(4, 44)
        service.set_channel_gate(4, ChannelGate.LOCKED)
        service.set_manual_universe(bytes([9]) * 512)
        self.assertEqual(service.manual_universe_snapshot()[3], 9)
        service.clear_manual_universe()
        self.assertEqual(service.manual_universe_snapshot()[3], 0)

    def test_priority_id_seed_is_used_before_submission(self):
        service = WirelessDmxService(
            DaemonConfig(virtual_port_path="/tmp/wireless-dmx-seed-test"),
            serial_factory=lambda: FakeSerial(),
            virtual_backend=LinuxPtyBackend("/tmp/wireless-dmx-seed-test"),
        )
        service.seed_priority_ids(0x12345678)
        self.assertEqual(service.send_manual(priority=True, repeat_count=1, ttl_seconds=1), 0x12345678)

    def test_priority_retry_increments_attempt_without_changing_id(self):
        service = WirelessDmxService(
            DaemonConfig(virtual_port_path="/tmp/wireless-dmx-retry-test",
                         priority_confirmation_window_ms=1500,
                         priority_retry_cooldown_min_seconds=0,
                         priority_retry_cooldown_max_seconds=0),
            serial_factory=lambda: FakeSerial(),
            virtual_backend=LinuxPtyBackend("/tmp/wireless-dmx-retry-test"),
        )
        priority_id = service.send_manual(priority=True, repeat_count=1, ttl_seconds=1)
        event = service._priority_events[priority_id]
        service.pacer._priority_queue.clear()
        now = event["last_attempt_at"] + 2.0
        service._service_priority_retries(now)
        service._service_priority_retries(event["retry_due_at"])
        self.assertEqual(service.snapshot().priority.retry_attempts, 1)
        self.assertEqual(service._priority_events[priority_id]["attempt"], 2)
        self.assertEqual(service._priority_events[priority_id]["expected_receivers"], set())
        self.assertFalse(service._priority_events[priority_id]["ack_complete"])

    def test_priority_retry_waits_for_configured_cooldown(self):
        service = WirelessDmxService(
            DaemonConfig(virtual_port_path="/tmp/wireless-dmx-retry-cooldown",
                         priority_confirmation_window_ms=1500,
                         priority_retry_cooldown_min_seconds=2,
                         priority_retry_cooldown_max_seconds=2),
            serial_factory=lambda: FakeSerial(),
            virtual_backend=LinuxPtyBackend("/tmp/wireless-dmx-retry-cooldown"),
        )
        priority_id = service.send_manual(priority=True, repeat_count=1, ttl_seconds=1)
        event = service._priority_events[priority_id]
        service.pacer._priority_queue.clear()
        expired = event["last_attempt_at"] + 2.0
        service._service_priority_retries(expired)
        self.assertEqual(service.snapshot().priority.retry_attempts, 0)
        self.assertIsNotNone(event["retry_due_at"])
        service._service_priority_retries(event["retry_due_at"] - 0.001)
        self.assertEqual(service.snapshot().priority.retry_attempts, 0)
        service._service_priority_retries(event["retry_due_at"])
        self.assertEqual(service.snapshot().priority.retry_attempts, 1)

    def test_priority_ack_on_retry_recovers_same_receiver_event(self):
        fake = FakeSerial()
        service = WirelessDmxService(
            DaemonConfig(virtual_port_path="/tmp/wireless-dmx-retry-ack-test"),
            serial_factory=lambda: fake,
            virtual_backend=LinuxPtyBackend(),
        )
        service._priority_submissions[42] = time.monotonic()
        service._priority_events[42] = {
            "universe": bytes(512), "repeat_count": 1, "ttl_seconds": 1.0,
            "reason": "test", "attempt": 2, "last_attempt_at": time.monotonic(),
            "retry_count": 1, "terminal": False, "expected_receivers": {7},
            "ack_complete": False, "ack_receivers": set(),
            "first_attempt_ack_receivers": set(), "ack_completed_at": None,
        }
        record = ACK_RECORD.pack(42, 7, 101, 2, 1, 1, -41, 1234, 37)
        payload = ACK_HEADER.pack(1, 1, 7, 1, 0, 0, 0) + record
        body = bytes((1, MANAGEMENT_PRIORITY_ACKS)) + struct.pack("<H", len(payload)) + payload
        frame = MANAGEMENT_SYNC + body + struct.pack("<H", crc16_ccitt(body))
        service._on_transmitter_data(frame)
        priority = service.snapshot().priority
        self.assertEqual(priority.ack_records_received, 1)
        self.assertEqual(priority.retry_recovered, 1)
        self.assertEqual(priority.ack_duplicate_records, 0)
        self.assertTrue(service._priority_events[42]["ack_complete"])
        self.assertEqual(service._priority_events[42]["ack_receivers"], {7})

    def test_gate_priority_requires_gate_applied_ack_status(self):
        service = WirelessDmxService(
            DaemonConfig(virtual_port_path="/tmp/wireless-dmx-gate-ack-status"),
            serial_factory=lambda: FakeSerial(), virtual_backend=LinuxPtyBackend(),
        )
        service._priority_submissions[42] = time.monotonic()
        service._priority_events[42] = {
            "universe": bytes(512), "repeat_count": 1, "ttl_seconds": 5.0,
            "reason": "gate", "attempt": 1, "last_attempt_at": time.monotonic(),
            "retry_count": 0, "terminal": False, "terminal_reason": None,
            "transmission_complete": True, "ack_complete": False,
            "hard_gate_mask": bytes(64), "expected_receivers": {7},
            "ack_receivers": set(), "gate_applied_receivers": set(),
            "first_attempt_ack_receivers": set(), "ack_completed_at": None,
            "receiver_states": {7: {"attempt": 1, "started_at": time.monotonic(),
                                    "ack": False, "failed": False}},
            "receiver_order": [7], "receiver_index": 0, "current_receiver": 7,
        }
        record = ACK_RECORD.pack(42, 7, 101, 1, 1, 1, -41, 1234, 37)
        payload = ACK_HEADER.pack(1, 1, 7, 1, 0, 0, 0) + record
        body = bytes((1, MANAGEMENT_PRIORITY_ACKS)) + struct.pack("<H", len(payload)) + payload
        service._on_transmitter_data(MANAGEMENT_SYNC + body + struct.pack("<H", crc16_ccitt(body)))
        self.assertFalse(service._priority_events[42]["ack_complete"])

    def test_late_ack_upgrades_receiver_timeout_to_success(self):
        service = WirelessDmxService(
            DaemonConfig(virtual_port_path="/tmp/wireless-dmx-late-ack"),
            serial_factory=lambda: FakeSerial(), virtual_backend=LinuxPtyBackend(),
        )
        service._priority_submissions[42] = time.monotonic()
        service._priority_events[42] = {
            "universe": bytes(512), "repeat_count": 1, "ttl_seconds": 1.0,
            "reason": "test", "attempt": 1, "last_attempt_at": time.monotonic(),
            "retry_count": 0, "terminal": True, "terminal_reason": "receiver_timeout",
            "transmission_complete": True, "ack_complete": False,
            "expected_receivers": {7}, "ack_receivers": set(),
            "first_attempt_ack_receivers": set(), "ack_completed_at": None,
            "receiver_states": {7: {"attempt": 1, "started_at": time.monotonic(),
                                    "ack": False, "failed": True}},
            "receiver_order": [7], "receiver_index": 1, "current_receiver": None,
        }
        record = ACK_RECORD.pack(42, 7, 101, 1, 1, 1, -41, 1234, 37)
        payload = ACK_HEADER.pack(1, 1, 7, 1, 0, 0, 0) + record
        body = bytes((1, MANAGEMENT_PRIORITY_ACKS)) + struct.pack("<H", len(payload)) + payload
        frame = MANAGEMENT_SYNC + body + struct.pack("<H", crc16_ccitt(body))
        service._on_transmitter_data(frame)
        event = service._priority_events[42]
        self.assertTrue(event["ack_complete"])
        self.assertEqual(event["terminal_reason"], "ack_complete")
        self.assertFalse(event["receiver_states"][7]["failed"])

    def test_management_queue_does_not_evict_dmx(self):
        fake = FakeSerial()
        from wireless_dmx.transmitter.connection import TransmitterConnection
        connection = TransmitterConnection(DaemonConfig(), lambda data: None, lambda: fake)
        connection.send_latest(b"dmx")
        connection.send_immediate(b"mgmt")
        connection.start()
        deadline = time.monotonic() + 1
        while time.monotonic() < deadline and len(fake.writes) < 2:
            time.sleep(0.01)
        connection.stop()
        self.assertEqual(fake.writes[:2], [b"mgmt", b"dmx"])

    def test_management_queue_preserves_priority_marker_order(self):
        fake = FakeSerial()
        from wireless_dmx.transmitter.connection import TransmitterConnection
        connection = TransmitterConnection(DaemonConfig(), lambda data: None, lambda: fake)
        connection.send_immediate(b"marker")
        connection.send_immediate(b"ack-poll")
        connection.start()
        deadline = time.monotonic() + 1
        while time.monotonic() < deadline and len(fake.writes) < 2:
            time.sleep(0.01)
        connection.stop()
        self.assertEqual(fake.writes[:2], [b"marker", b"ack-poll"])

    def test_telemetry_request_is_reissued_after_timeout(self):
        fake = FakeSerial()
        service = WirelessDmxService(
            DaemonConfig(virtual_port_path="/tmp/wireless-dmx-telemetry-timeout",
                         telemetry_interval_seconds=0.05,
                         telemetry_response_timeout_seconds=0.01),
            serial_factory=lambda: fake,
            virtual_backend=LinuxPtyBackend("/tmp/wireless-dmx-telemetry-timeout"),
        )
        service.start()
        try:
            mode_body = bytes((1, 0x88, 2, 0, 0, 0))
            cache_body = bytes((1, MANAGEMENT_CACHE_CLEARED, 0, 0))
            fake.reads.append(
                MANAGEMENT_SYNC + mode_body + struct.pack("<H", crc16_ccitt(mode_body)) +
                MANAGEMENT_SYNC + cache_body + struct.pack("<H", crc16_ccitt(cache_body)))
            deadline = time.monotonic() + 2.0
            while time.monotonic() < deadline and service.snapshot().telemetry.requests_sent < 3:
                time.sleep(0.01)
            snapshot = service.snapshot()
            self.assertGreaterEqual(snapshot.telemetry.requests_sent, 3)
            self.assertGreaterEqual(snapshot.telemetry.consecutive_failures, 1)
            self.assertLessEqual(snapshot.telemetry.requests_sent, 8)
        finally:
            service.stop()

    def test_telemetry_report_clears_in_flight_request(self):
        fake = FakeSerial()
        service = WirelessDmxService(
            DaemonConfig(virtual_port_path="/tmp/wireless-dmx-telemetry-success"),
            serial_factory=lambda: fake,
            virtual_backend=LinuxPtyBackend("/tmp/wireless-dmx-telemetry-success"),
        )
        service._telemetry_request_started = time.monotonic()
        service._telemetry_requests_sent = 1
        service._on_transmitter_data(telemetry_part())
        # The report is complete and should be counted even when injected by a
        # fake transport rather than received by the background thread.
        self.assertEqual(service.snapshot().telemetry.reports_received, 1)
        self.assertFalse(service.snapshot().telemetry.request_in_flight)


if __name__ == "__main__":
    unittest.main()
