aidancrowther/DMX-Now/Host Software/wireless_dmx_daemon/tests/run_30min_acceptance.py

#!/usr/bin/env python3
"""End-to-end 30-minute daemon acceptance test using the real Mega monitor.

This runner is intentionally outside the package test suite because it uses
real serial devices. It opens the daemon's Linux PTY as a lighting client,
streams a stable full-universe ENTTEC ramp at 20 Hz, and verifies the receiver
output using the Arduino Mega on its USB serial port.
"""

from __future__ import annotations

import argparse
import json
import os
import sys
import time
from pathlib import Path

import serial

ROOT = Path(__file__).resolve().parents[1]
sys.path.insert(0, str(ROOT))

from wireless_dmx.app import WirelessDmxService
from wireless_dmx.enttec.protocol import encode_dmx
from wireless_dmx.models import DaemonConfig
from wireless_dmx.virtual_serial.factory import create_pty_backend


def wait_line(port: serial.Serial, prefix: str, timeout: float) -> str:
    deadline = time.monotonic() + timeout
    seen: list[str] = []
    while time.monotonic() < deadline:
        line = port.readline().decode(errors="replace").strip()
        if line:
            seen.append(line)
        if line.startswith(prefix):
            return line
    raise TimeoutError(f"waiting for {prefix!r}; seen={seen[-10:]!r}")


def send_mega_command(port: serial.Serial, text: str, prefix: str, timeout: float = 5.0) -> str:
    port.write((text + "\n").encode())
    port.flush()
    return wait_line(port, prefix, timeout)


def parse_mega_result(line: str) -> dict[str, int]:
    values: dict[str, int] = {}
    for token in line.split()[1:]:
        if "=" in token:
            key, value = token.split("=", 1)
            values[key] = int(value.rstrip("ms"))
    return values


def main() -> int:
    parser = argparse.ArgumentParser(description=__doc__)
    parser.add_argument("--tx-port", default="/dev/ttyUSB0")
    parser.add_argument("--mega-port", default="/dev/ttyUSB1")
    parser.add_argument("--seconds", type=int, default=1800)
    parser.add_argument("--telemetry-interval", type=float, default=15.0)
    parser.add_argument("--priority-interval", type=float, default=60.0)
    parser.add_argument("--priority-events", type=int, default=30)
    parser.add_argument("--priority-drain-seconds", type=float, default=5.0)
    parser.add_argument("--expected-receiver", action="append", type=lambda value: int(value, 0),
                        help="receiver ID expected throughout the run; may be repeated")
    parser.add_argument("--min-mega-checks-per-second", type=float, default=30.0)
    parser.add_argument("--run-dir", type=Path, required=True)
    args = parser.parse_args()
    if args.seconds < 1800:
        parser.error("--seconds must be at least 1800")

    args.run_dir.mkdir(parents=True, exist_ok=True)
    manifest_path = args.run_dir / "manifest.json"
    telemetry_path = args.run_dir / "daemon_telemetry.jsonl"
    progress_path = args.run_dir / "progress.jsonl"
    requested_path = f"/tmp/wireless-dmx-acceptance-{os.getpid()}"
    try:
        os.unlink(requested_path)
    except FileNotFoundError:
        pass

    summary: dict[str, object] = {
        "tx_port": args.tx_port,
        "mega_port": args.mega_port,
        "seconds_requested": args.seconds,
        "dmx_hz_requested": 20.0,
        "telemetry_interval_seconds": args.telemetry_interval,
        "priority_interval_seconds": args.priority_interval,
        "priority_events_requested": args.priority_events,
        "priority_drain_seconds": args.priority_drain_seconds,
        "expected_receivers": sorted(args.expected_receiver or []),
        "min_mega_checks_per_second": args.min_mega_checks_per_second,
        "priority_retry_cooldown_min_seconds": 1.0,
        "priority_retry_cooldown_max_seconds": 2.5,
        "passed": False,
    }
    priority_id_seed = (int(time.time()) ^ (os.getpid() << 16)) & 0xFFFFFFFF
    summary["priority_id_seed"] = priority_id_seed
    service: WirelessDmxService | None = None
    client: serial.Serial | None = None
    mega: serial.Serial | None = None
    tx_times: list[float] = []
    telemetry_reports = 0
    telemetry_records = 0
    priority_ids: list[int] = []
    next_priority = 0.0
    priority_waiting_for: int | None = None
    priority_wait_started = 0.0
    normal_frames_during_priority = 0
    normal_frames_before_priority = 0
    normal_frames_after_priority = 0
    telemetry_log = telemetry_path.open("w", encoding="utf-8")
    progress_log = progress_path.open("w", encoding="utf-8")
    started = time.monotonic()

    try:
        config = DaemonConfig(
            transmitter_device=args.tx_port,
            virtual_port_path=requested_path,
            pacer_enabled=True,
            pacer_rate_hz=20.0,
            telemetry_enabled=True,
            telemetry_interval_seconds=args.telemetry_interval,
            priority_confirmation_window_ms=1500,
            priority_retry_cooldown_min_seconds=1.0,
            priority_retry_cooldown_max_seconds=2.5,
        )
        service = WirelessDmxService(config, virtual_backend=create_pty_backend(requested_path))
        service.start()
        service.seed_priority_ids(priority_id_seed)
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
